xtremespb/frank/hardware/frank_rm1z/3D/Mini-DIN-6P.step

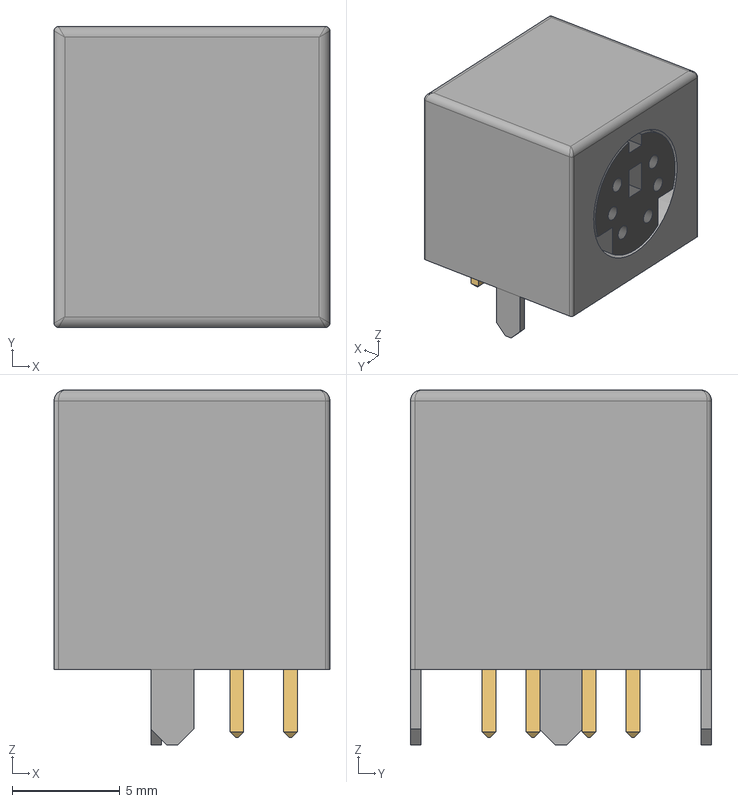
[picture p15: CAD file, 2024-08-21]
hardware/frank_rm1z/3D/Mini-DIN-6P.step
12.8 x 14.0 x 16.5 mm
