xtremespb/frank/hardware/frank_rm1z/3D/SJ1-3535NG.stp

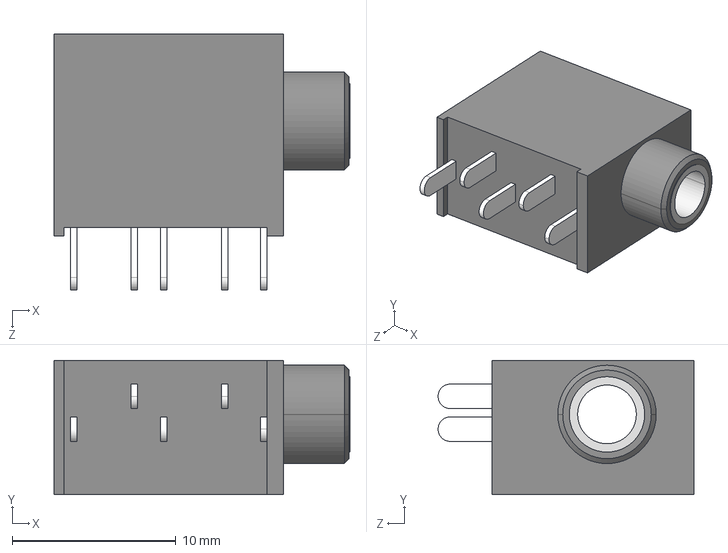
[picture p16: CAD file, 2024-08-21]
hardware/frank_rm1z/3D/SJ1-3535NG.stp
18.1 x 8.20 x 15.6 mm
