xtremespb/frank/hardware/frank_m2/DOCS/HR3FQ.pdf

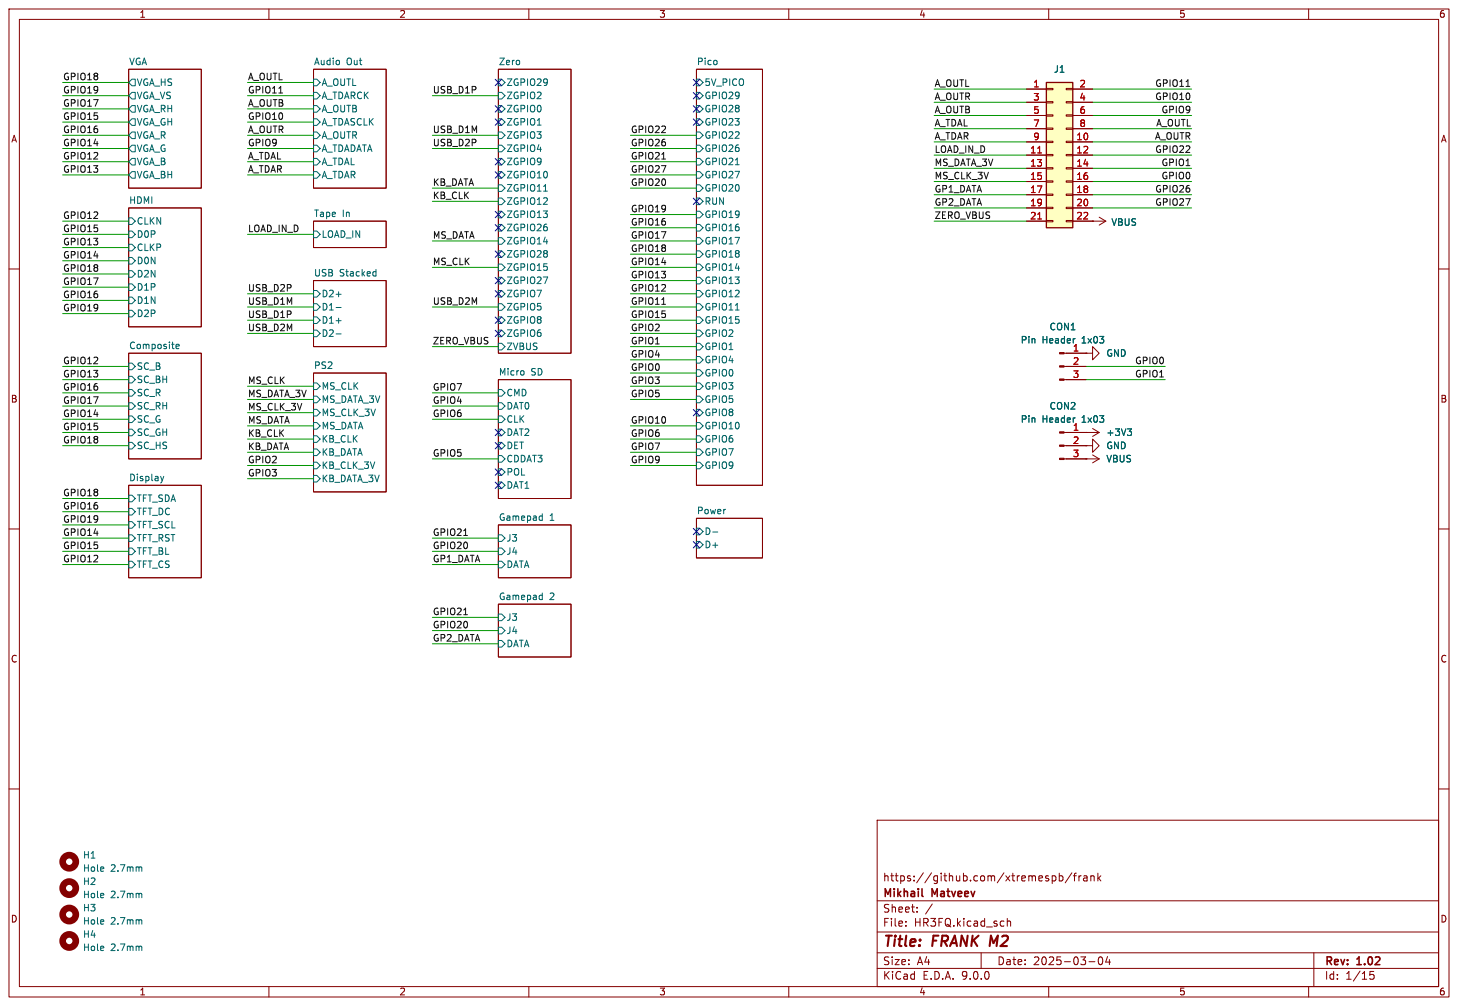
[picture p76: page 1]

ZERO_VBUS
DAT0 CLK DAT2 DET CDDAT3 POL DAT1 Micro SD

https://github.com/xtremespb/frank

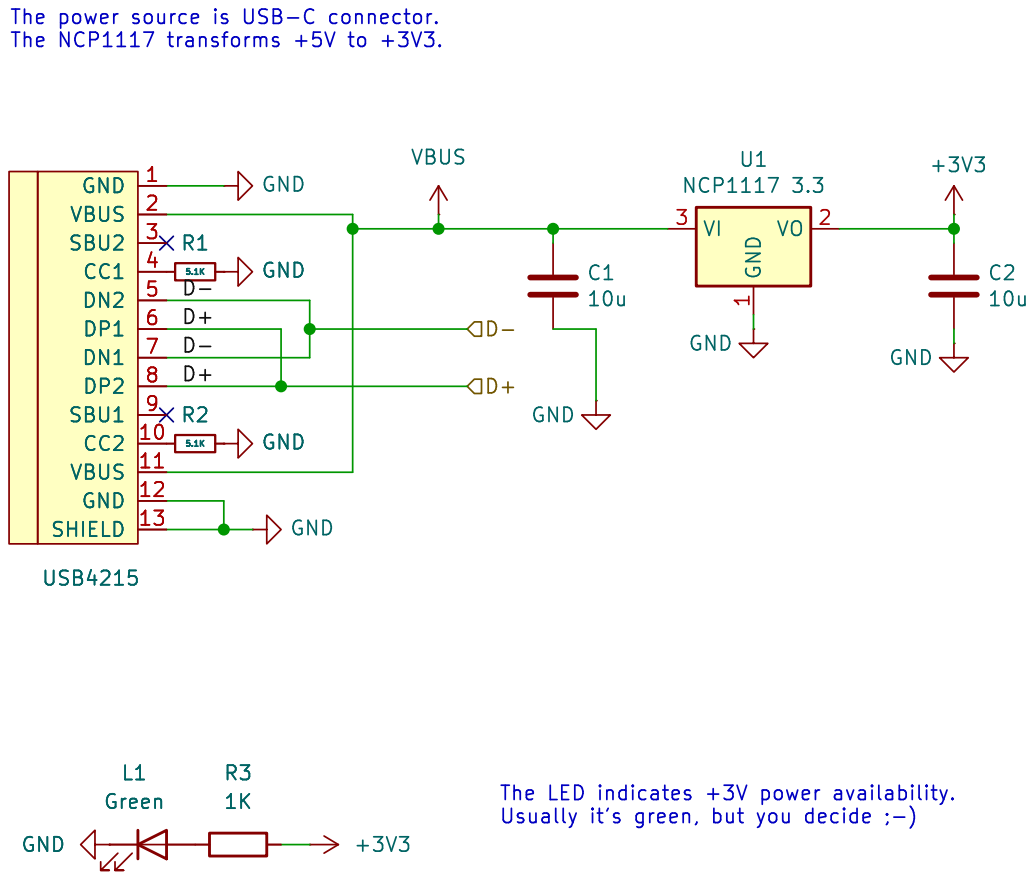
[picture p77: page 2]

1 VO 2 U1 GND NCP1117 3.3 D- D+ D+D+D- D- The power source is USB-C connector. The NCP1117 transforms +5V to +3V3. The LED indicates +3V power availability.
1K GND

Usually it's green, but you decide ;-) GND GND

https://github.com/xtremespb/frank

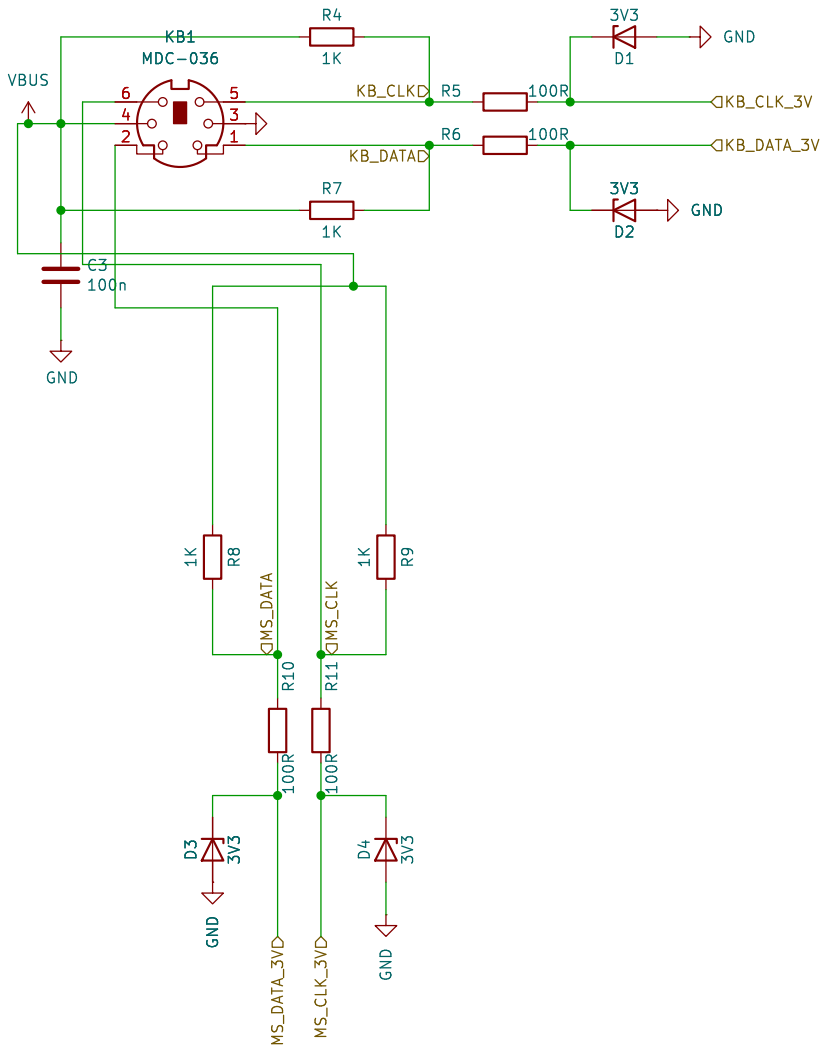
[picture p78: page 3]

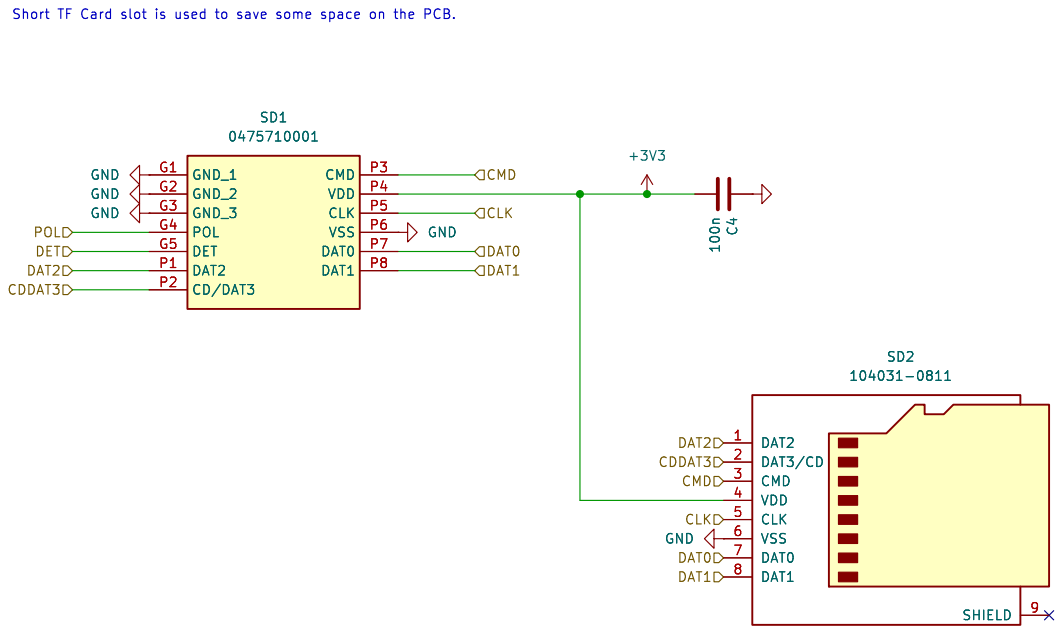
[picture p79: page 4]

https://github.com/xtremespb/frank


https://github.com/xtremespb/frank


https://github.com/xtremespb/frank

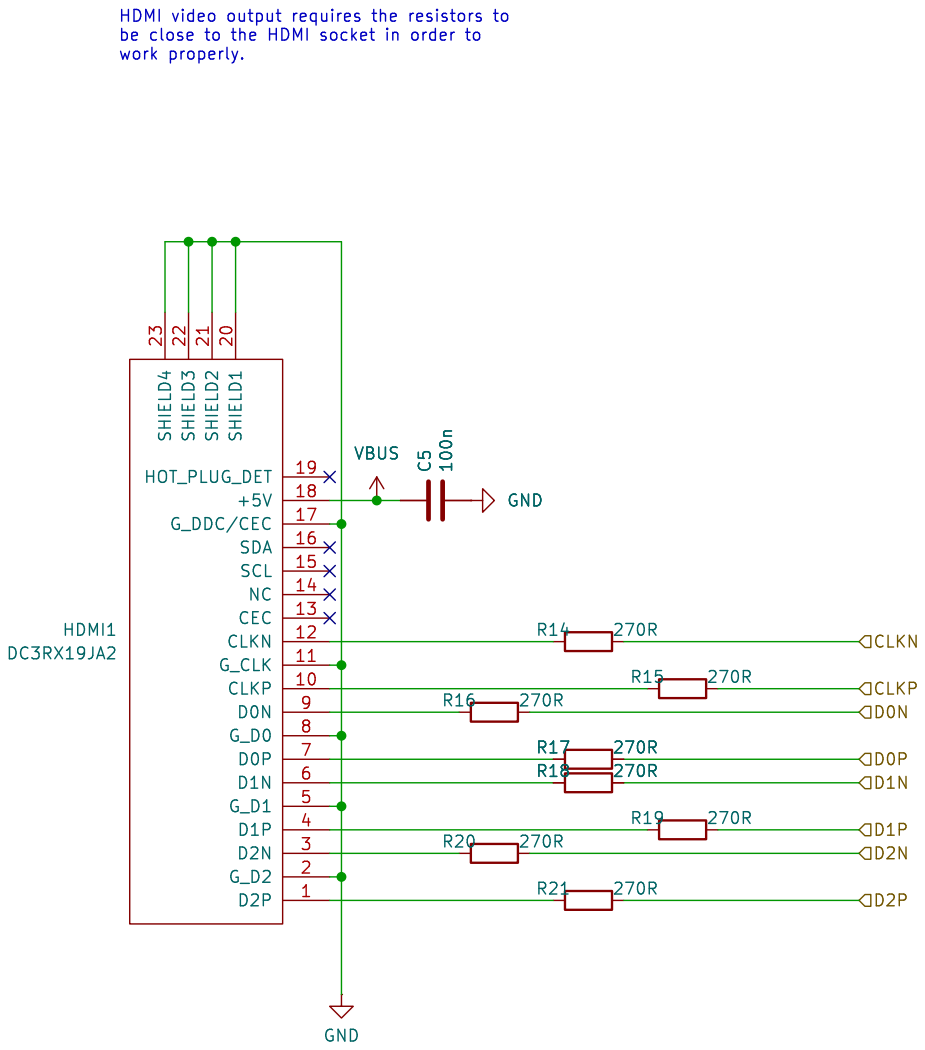
[picture p80: page 7]

https://github.com/xtremespb/frank


https://github.com/xtremespb/frank

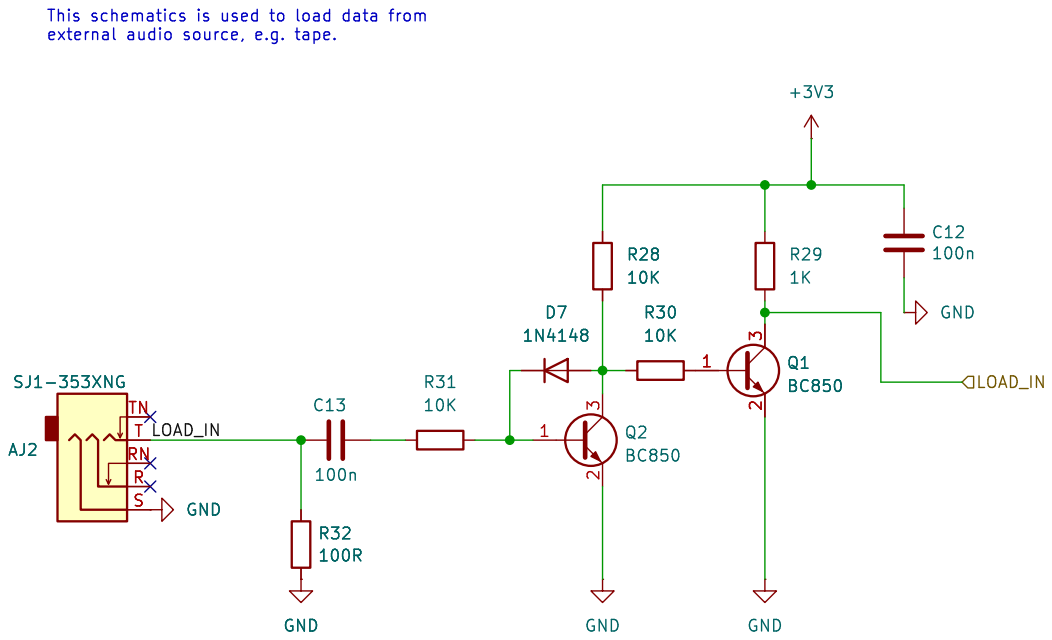
[picture p81: page 9]

https://github.com/xtremespb/frank

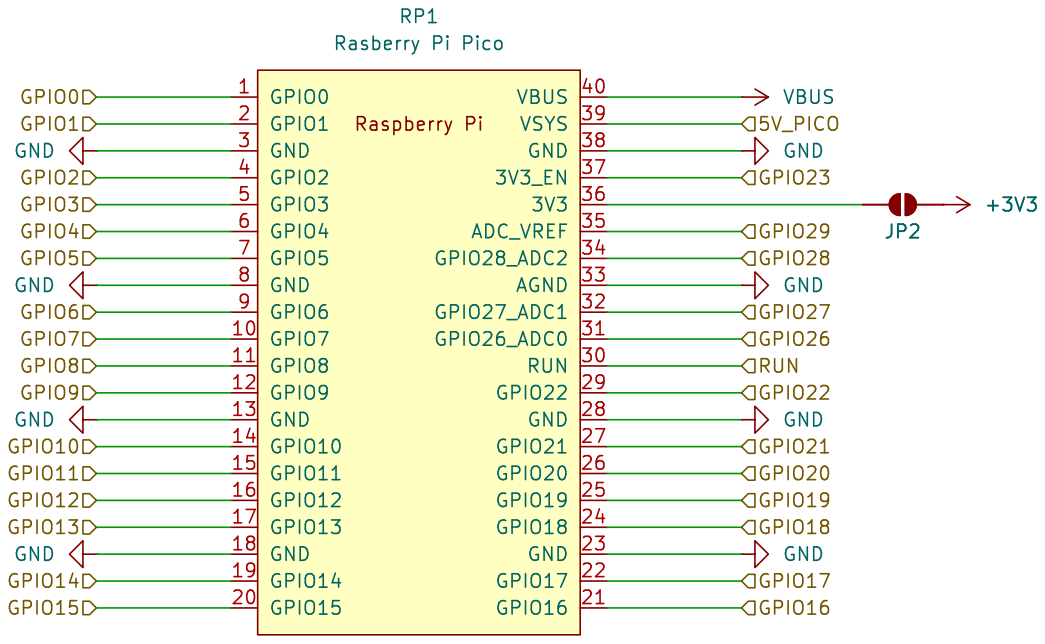
[picture p82: page 10]

https://github.com/xtremespb/frank


https://github.com/xtremespb/frank


https://github.com/xtremespb/frank


https://github.com/xtremespb/frank


https://github.com/xtremespb/frank


https://github.com/xtremespb/frank
