xtremespb/frank/hardware/hdmi2vga/DOCS/assembly.pdf

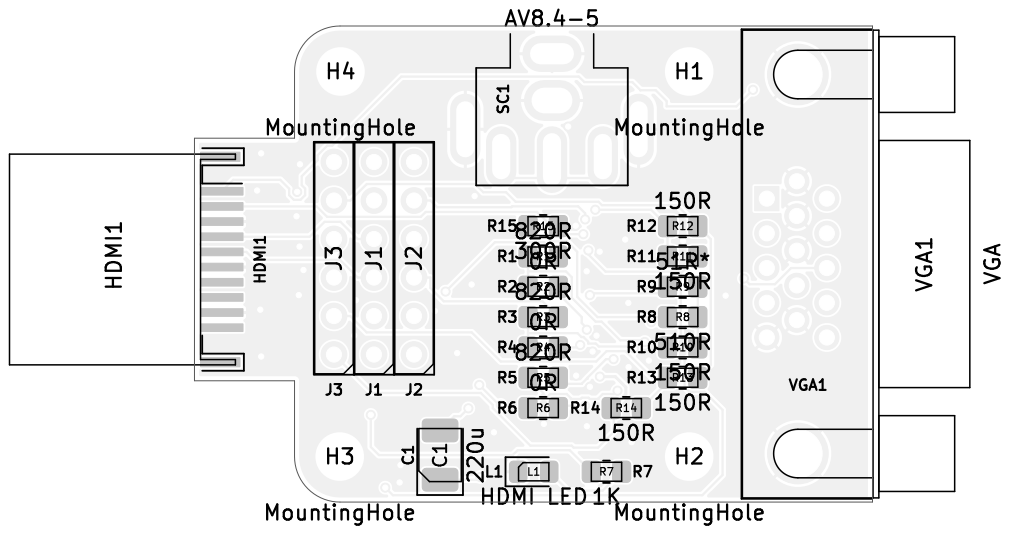
[picture p83: page 1]

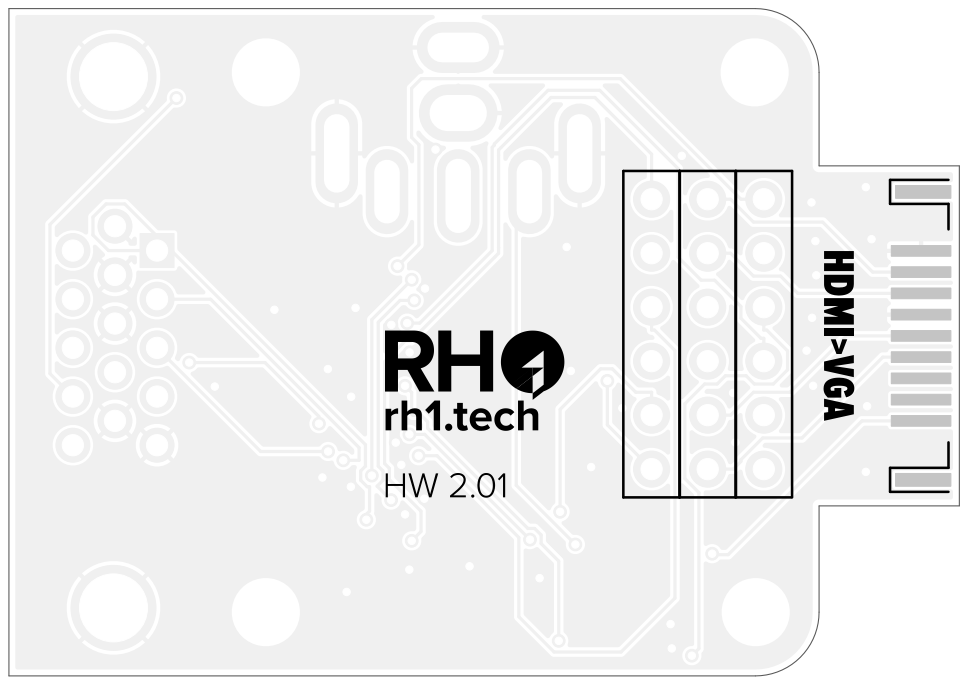
[picture p84: page 2]
D Date: 2025-03-04 KiCad; E.D.A. 9.0.0 Size: A4; Rev: 2.01; Id: /1 Title: HDMI to VGA Passive Adapter File: hdmi2vgaP.kicad_pcb Sheet: Black; And; White; BOT Mikhail; Matveev; https://github.com/xtremespb/frank Black; BOT -; Page 2/2
