xtremespb/frank/hardware/minifrank_rm1/DOCS/minifrank.pdf

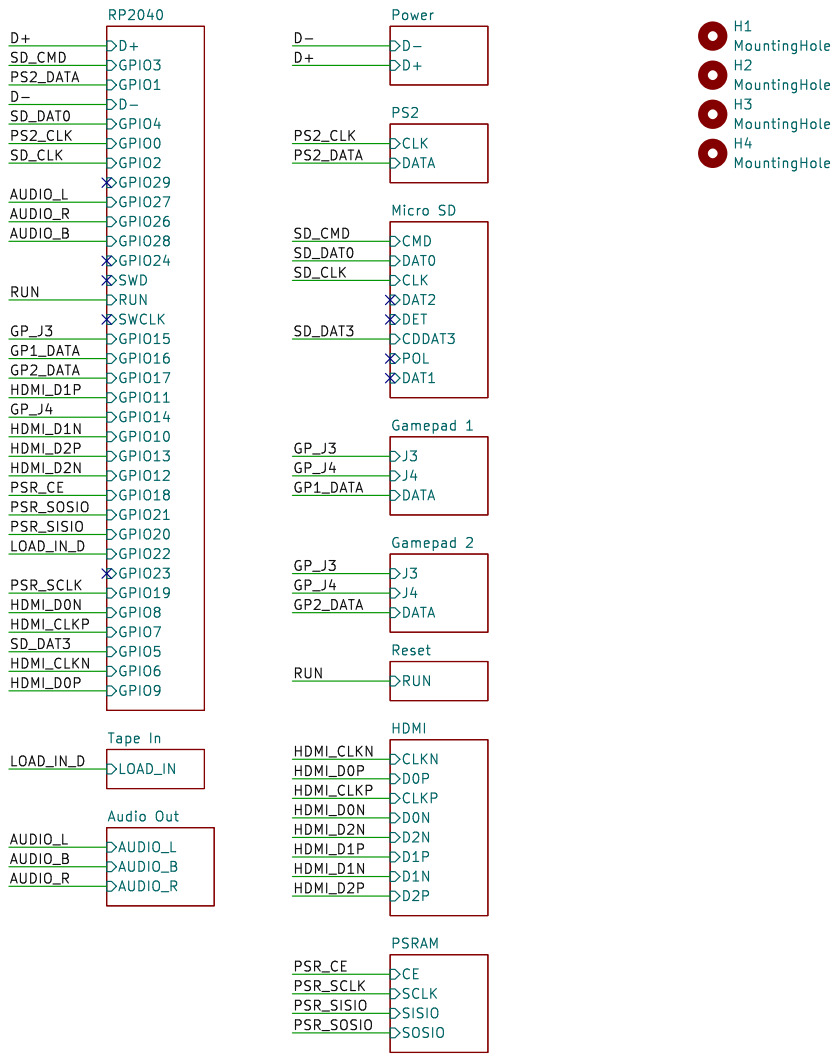
[picture p85: page 1]

H1 MountingHole H2 MountingHole H3 MountingHole H4 MountingHole AUDIO_R
SD_CMD

https://github.com/xtremespb/frank

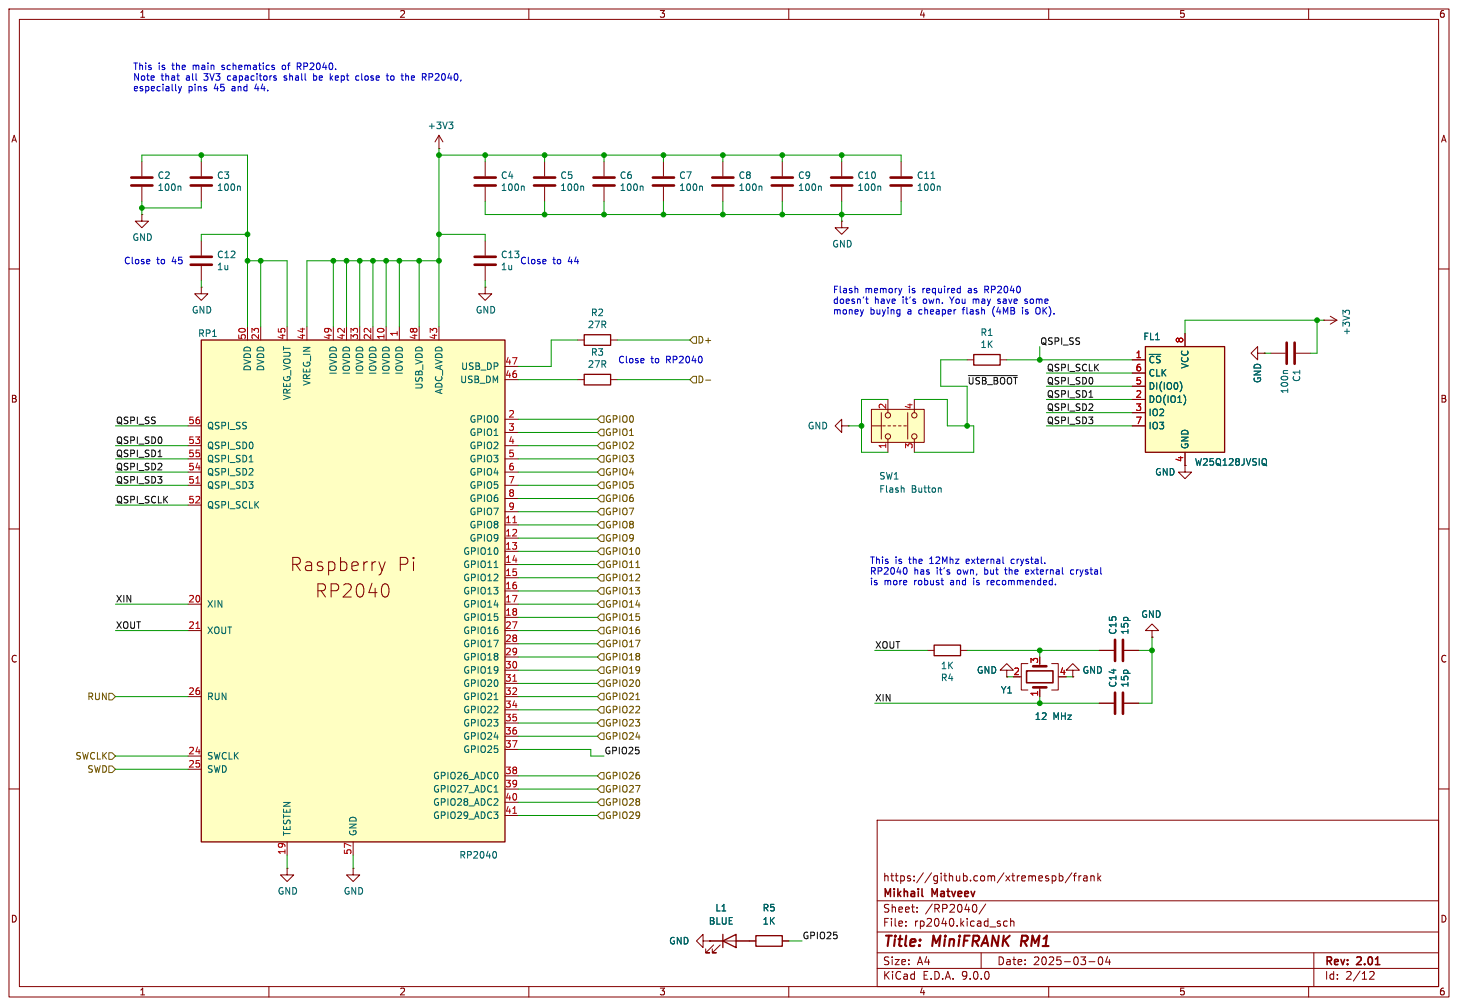
[picture p86: page 2]

https://github.com/xtremespb/frank

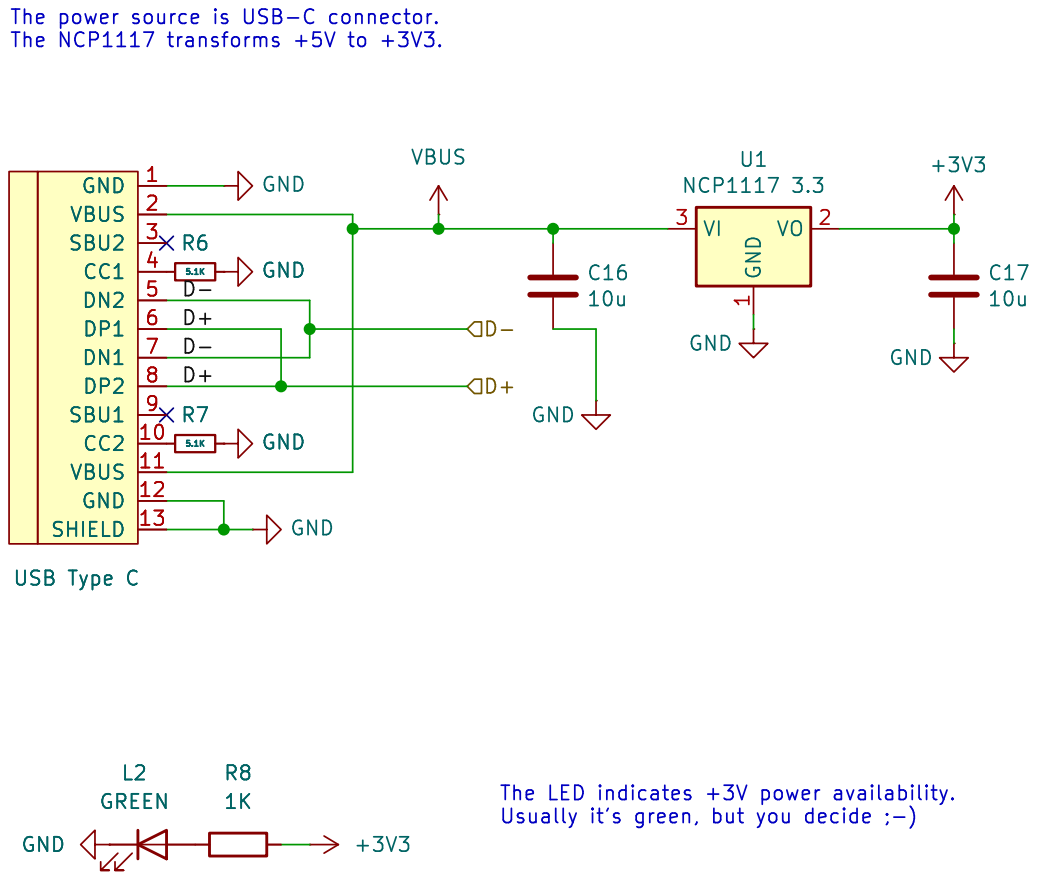
[picture p87: page 3]

https://github.com/xtremespb/frank

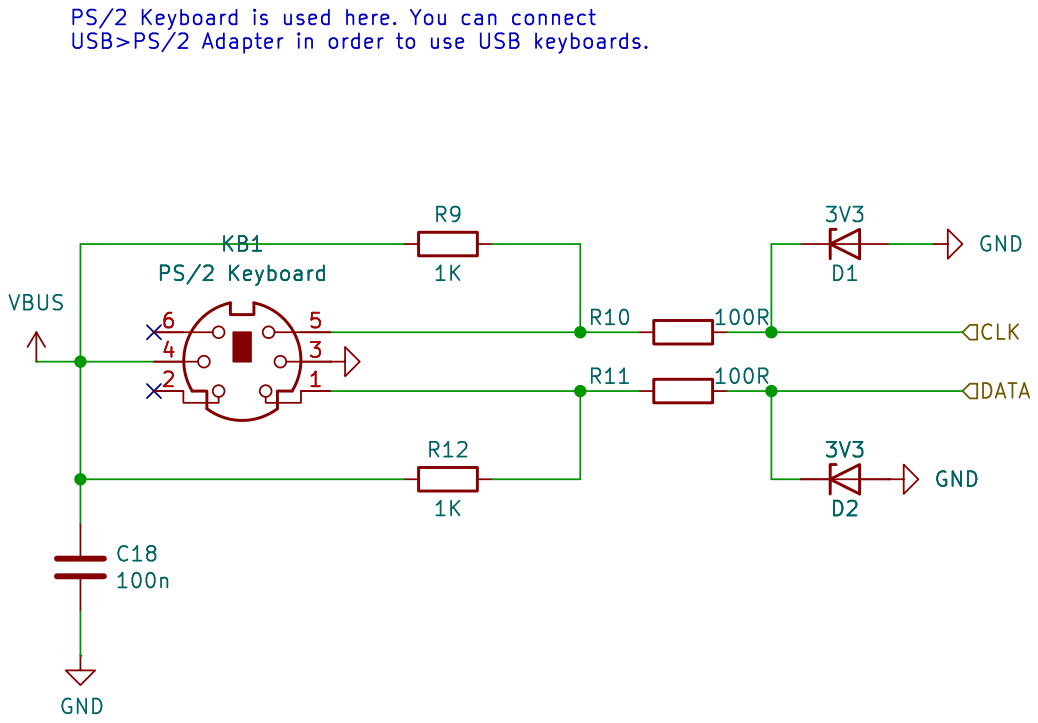
[picture p88: page 4]

https://github.com/xtremespb/frank

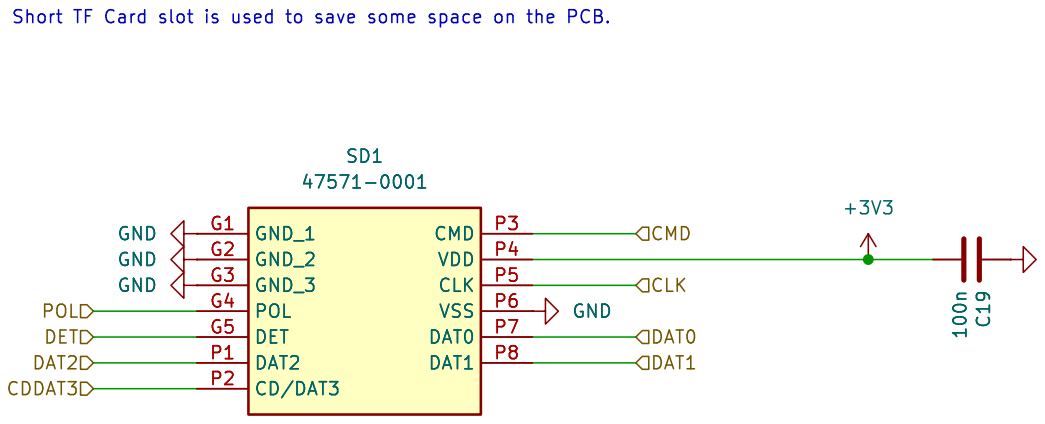
[picture p89: page 5]

https://github.com/xtremespb/frank

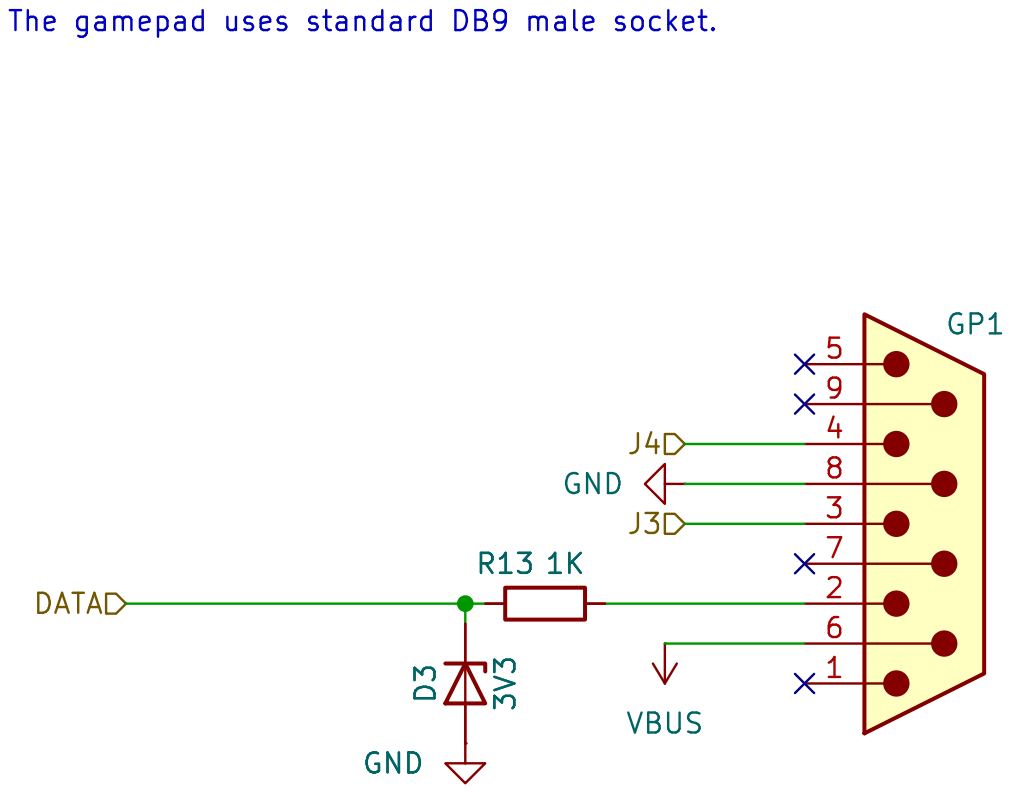
[picture p90: page 6]

https://github.com/xtremespb/frank

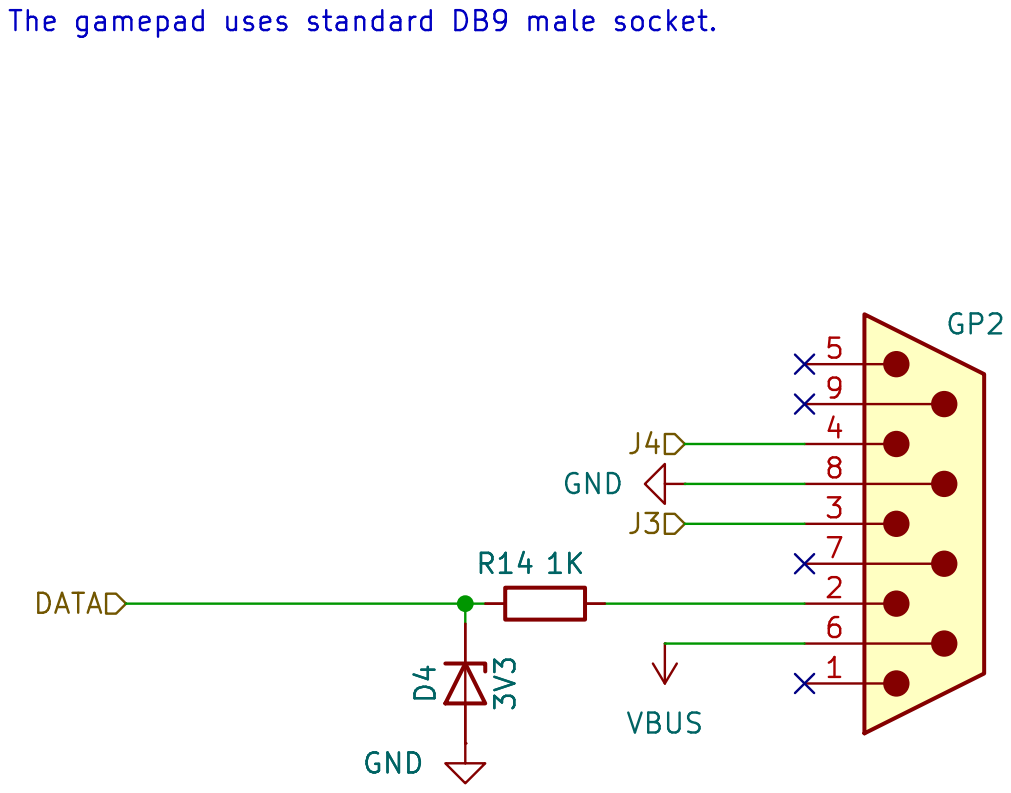
[picture p91: page 7]

https://github.com/xtremespb/frank

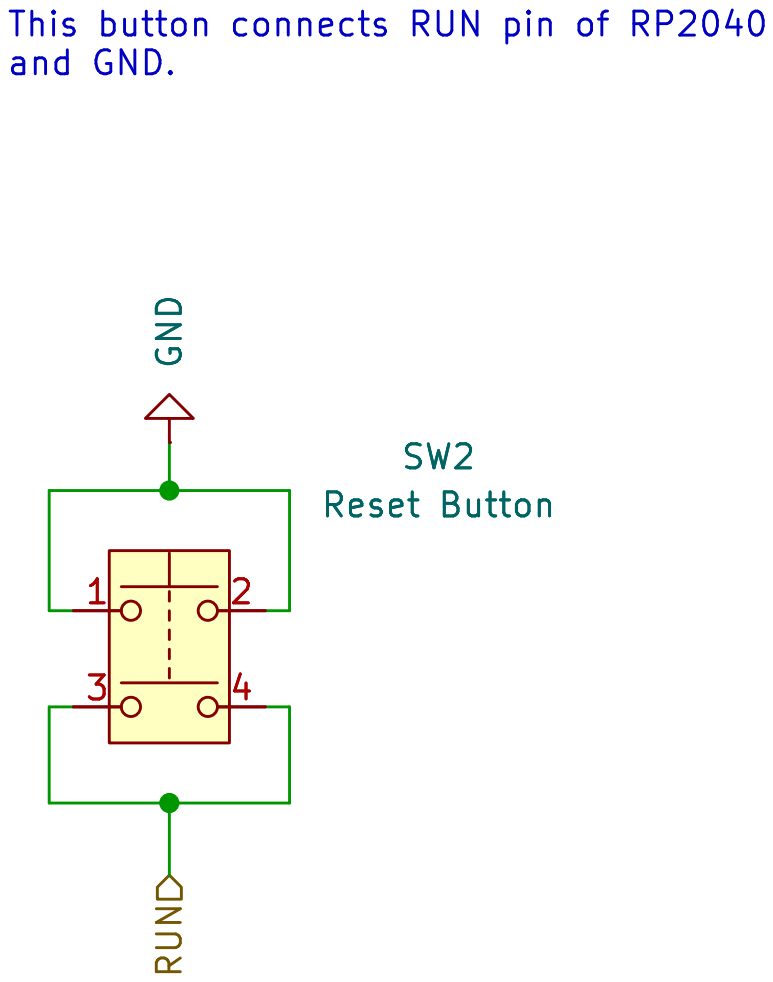
[picture p92: page 8]

https://github.com/xtremespb/frank

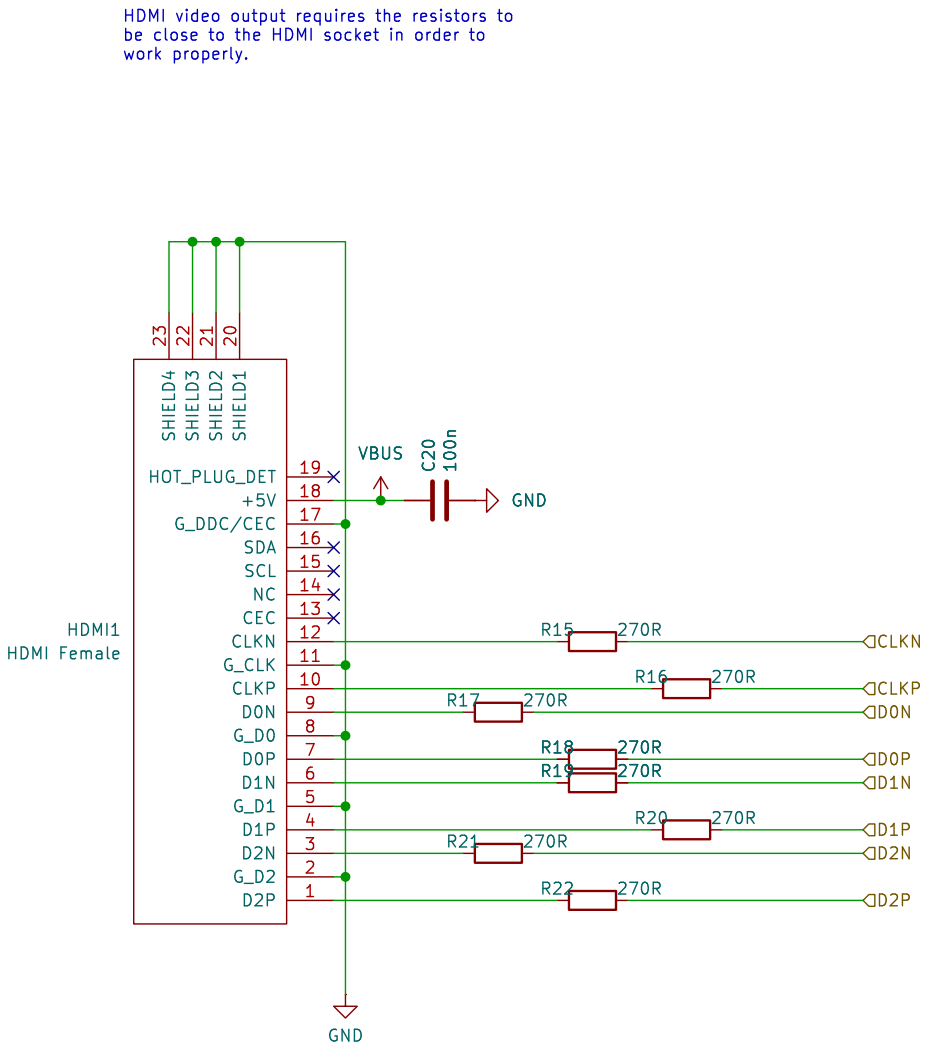
[picture p93: page 9]

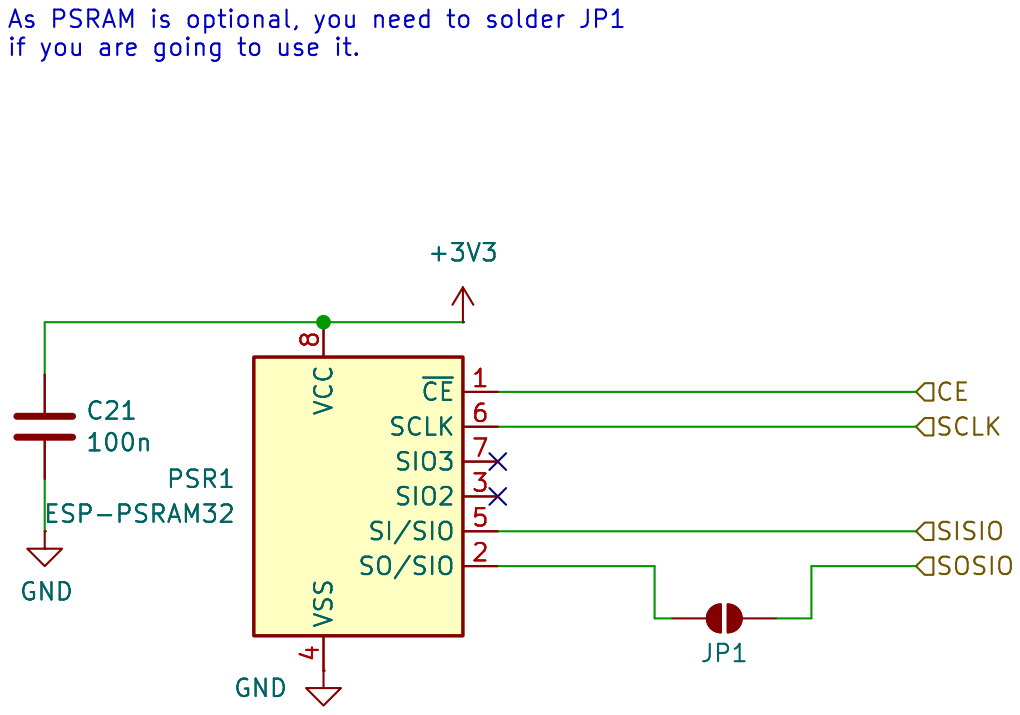
[picture p94: page 10]

if you are going to use it. GND

4 ~{CE}1 SCLK 6 SIO3 7 SIO2 3 SI/SIO 5 SO/SIO 2 PSR1 ESP-PSRAM32 GND

4 ~{CE}1 SCLK 6 SIO3 7 SIO2 3 SI/SIO 5 SO/SIO 2 GND

https://github.com/xtremespb/frank

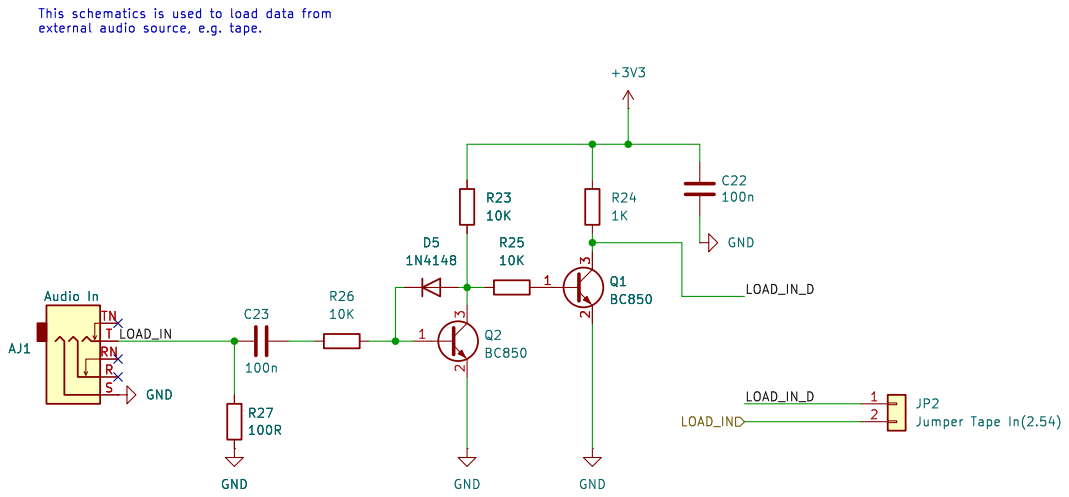
[picture p95: page 11]

https://github.com/xtremespb/frank

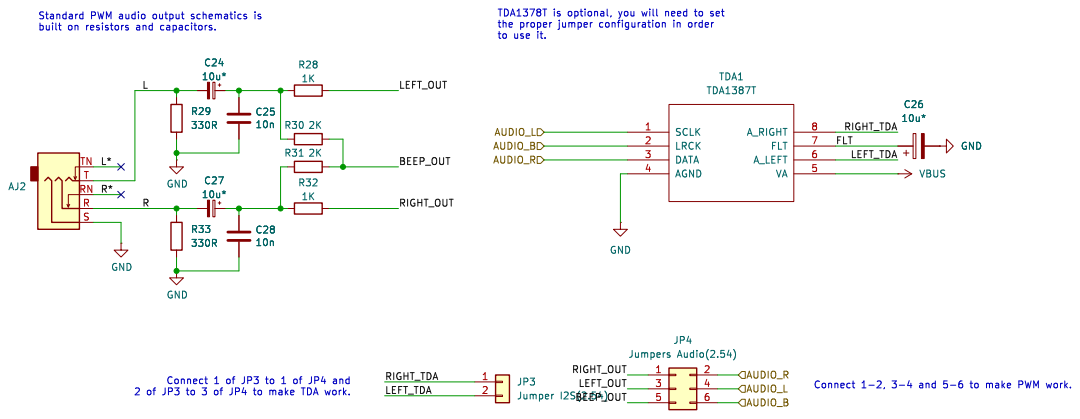
[picture p96: page 12]

to use it. Connect 1 of JP3 to 1 of JP4 and

https://github.com/xtremespb/frank
