xtremespb/frank/hardware/turbofrank/DOCS/turbofrank.pdf

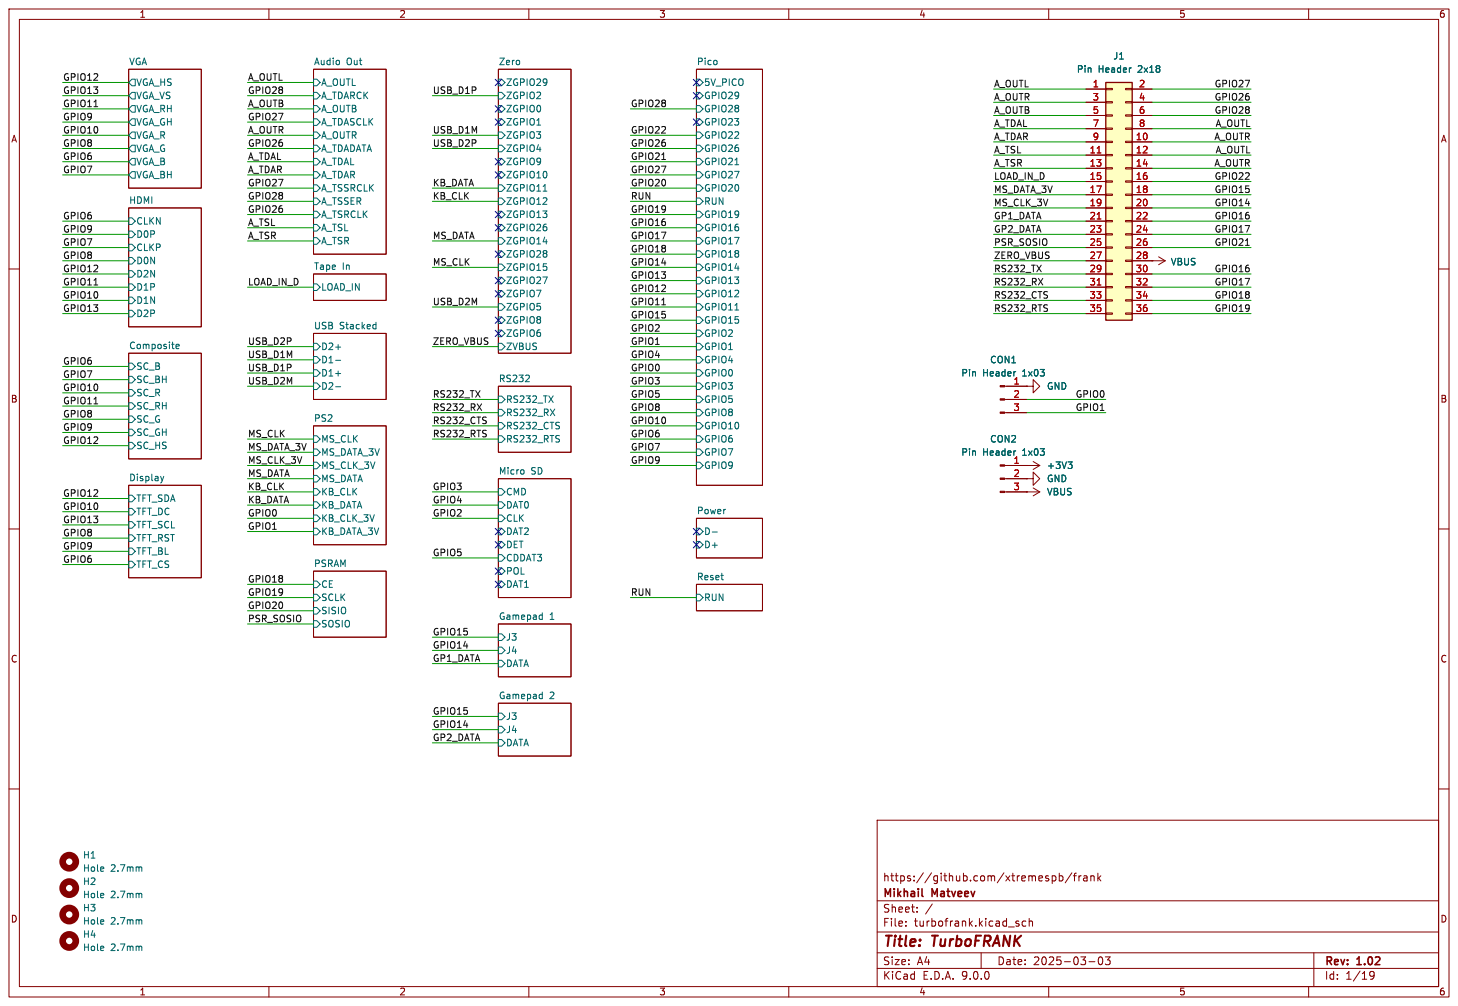
[picture p97: page 1]

J1 Pin Header 2x18 VBUS H3 Hole 2.7mm

DAT0 CLK DAT2 DET CDDAT3 POL DAT1 Micro SD

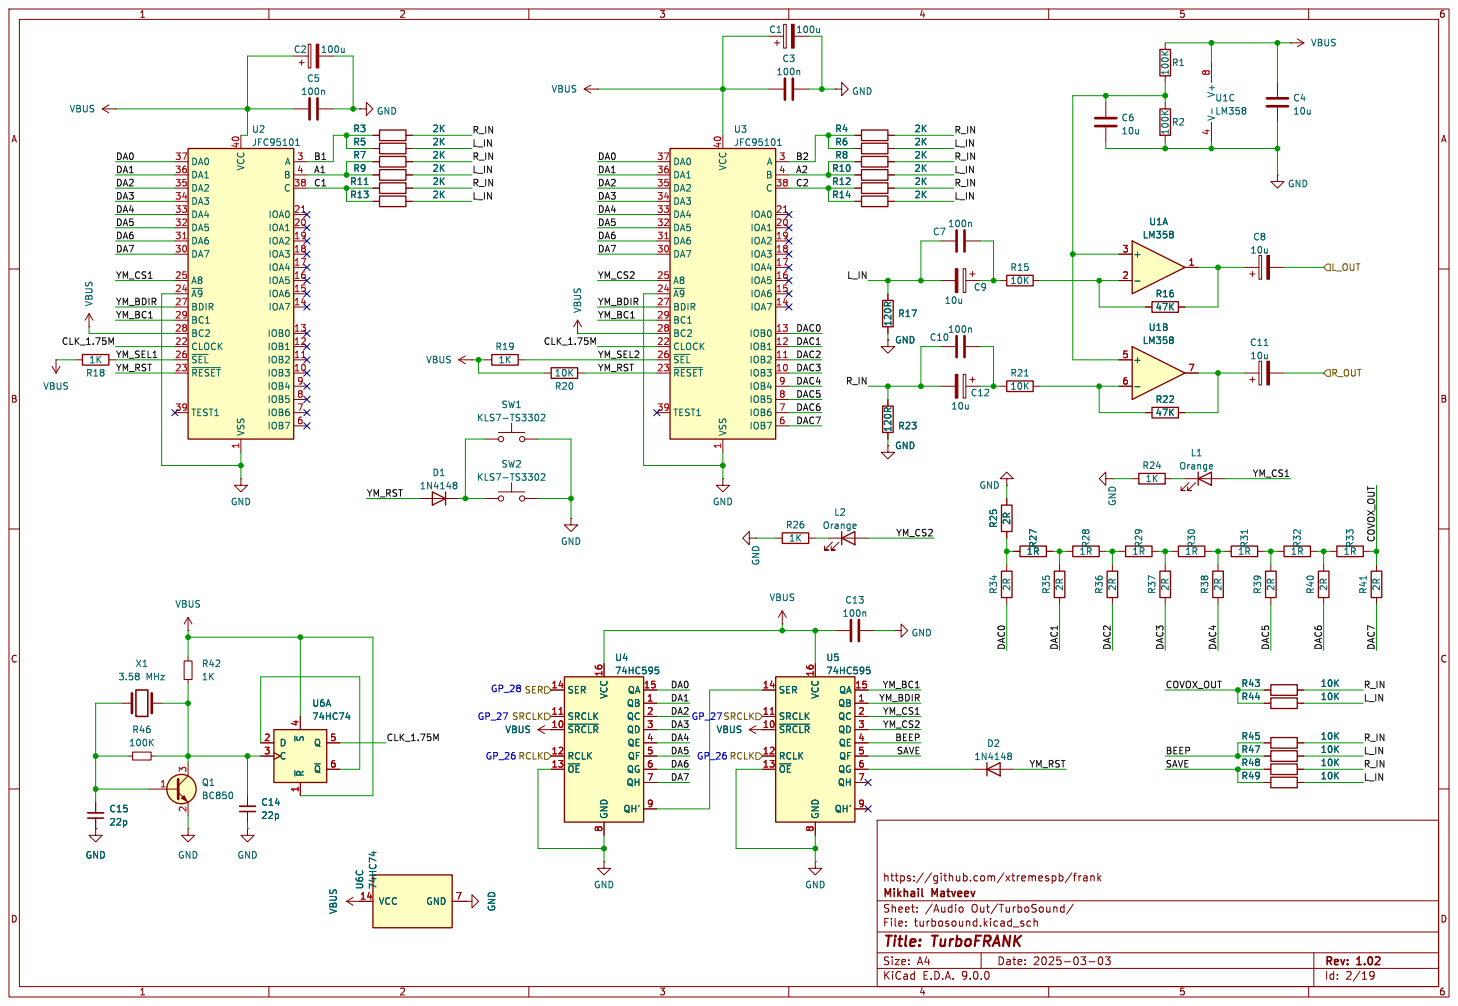
[picture p98: page 2]

8 QA 15 QB 1 QC 2 QD 3 QE 4 QF 5 QG 6 QH 7 QH' 9 VBUSU6C 74HC74 VCC 14 GND 7 GND R25 2R

SER

8 QA 15 QB 1 QC 2 QD 3 QE 4 QF 5 QG 6 QH 7 QH' 9 VBUS R45 10K R49 10K R47 10K R48 10K R44 10K R43 10K

https://github.com/xtremespb/frank

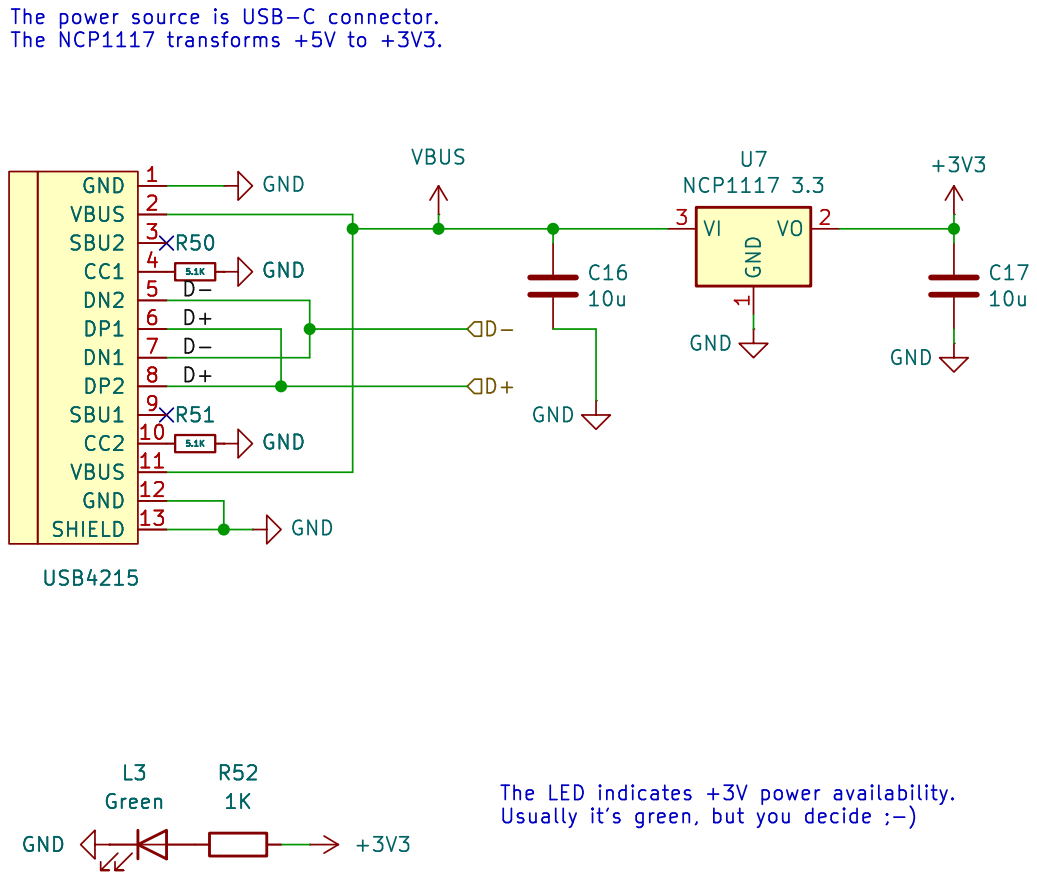
[picture p99: page 3]

1 VO 2 U7 NCP1117 3.3 +3V3 D- D+ D- D- D+D+ The power source is USB-C connector. The NCP1117 transforms +5V to +3V3. The LED indicates +3V power availability.

Usually it's green, but you decide ;-) GND

https://github.com/xtremespb/frank

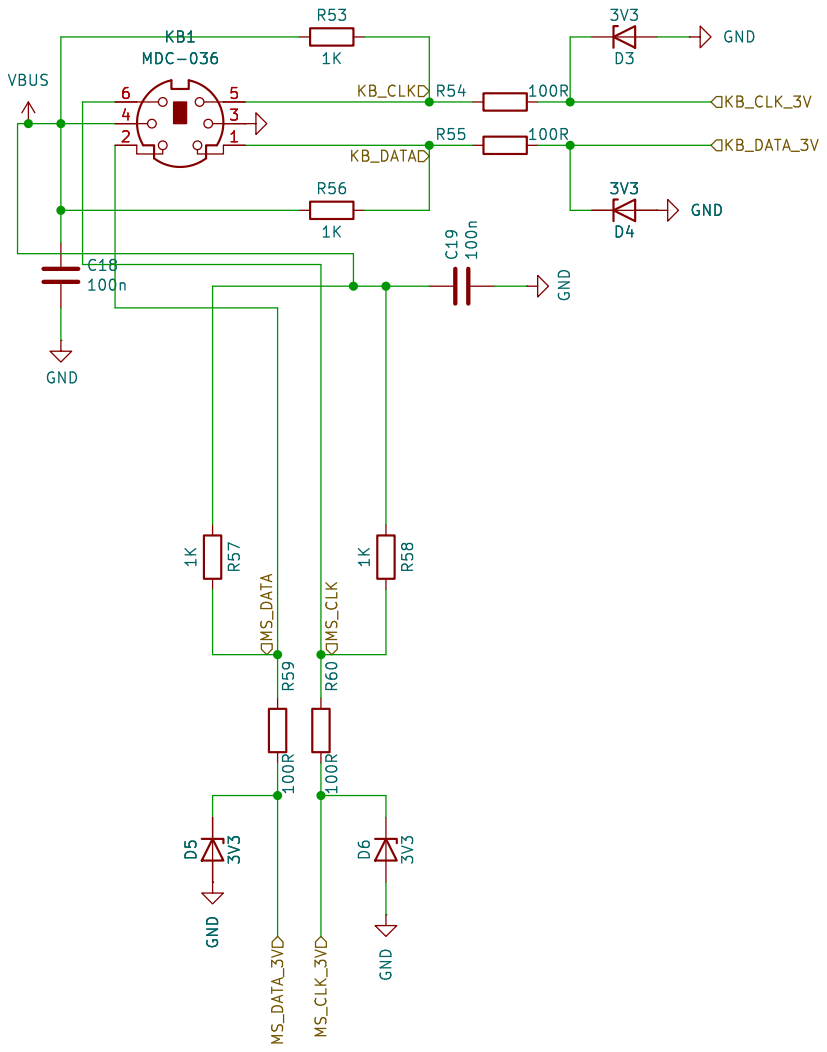
[picture p100: page 4]

https://github.com/xtremespb/frank

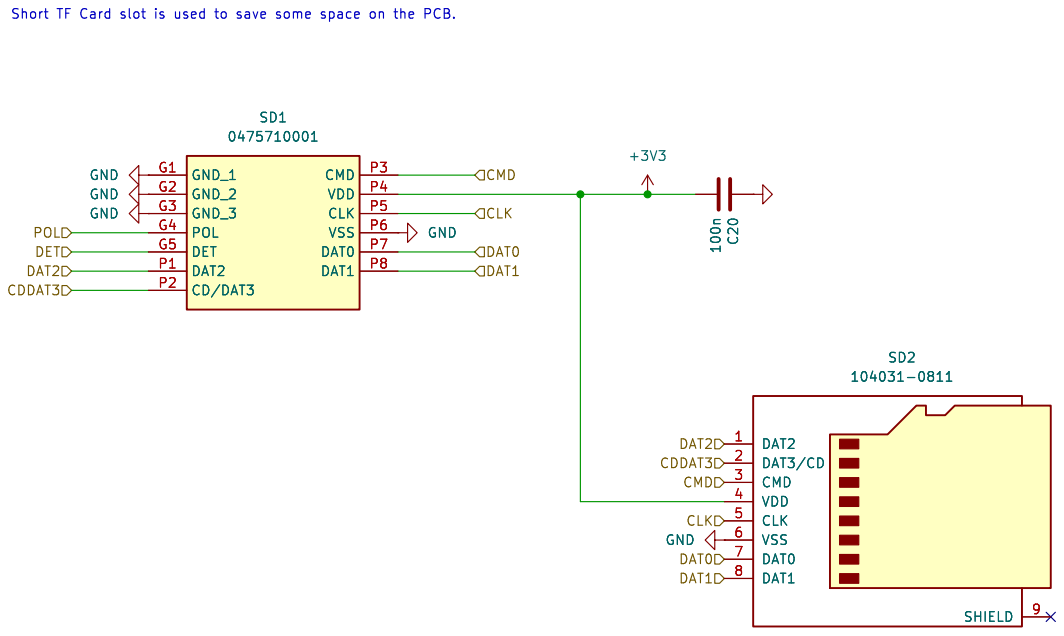
[picture p101: page 5]

https://github.com/xtremespb/frank

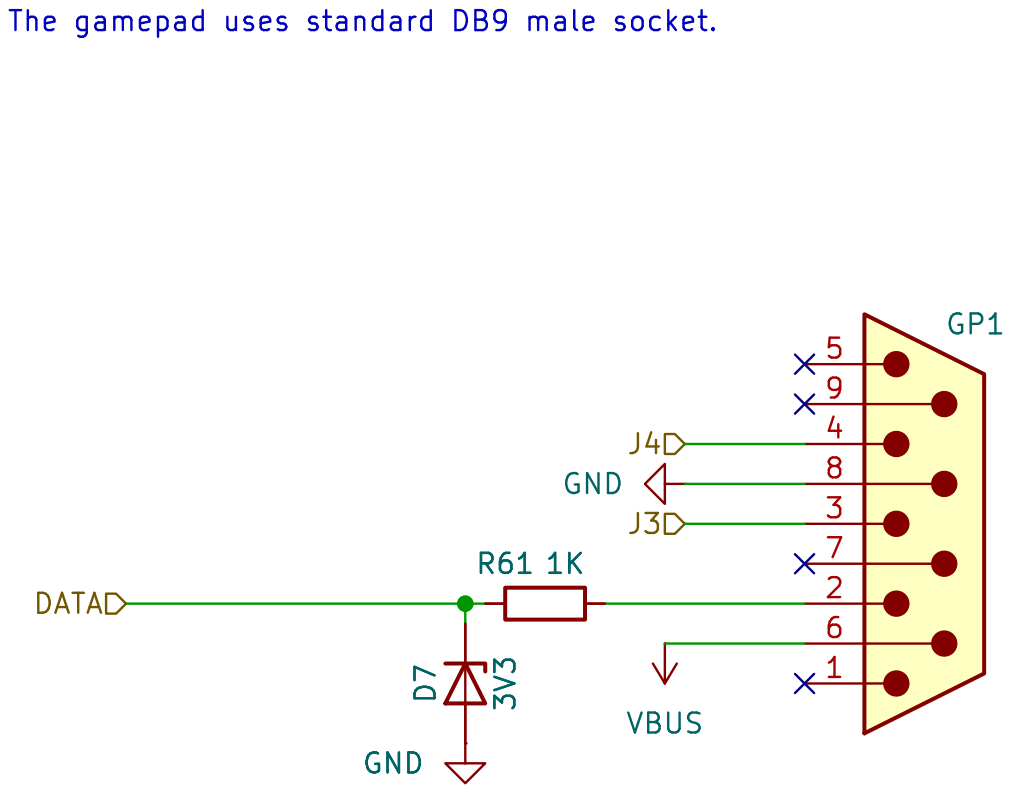
[picture p102: page 6]

https://github.com/xtremespb/frank

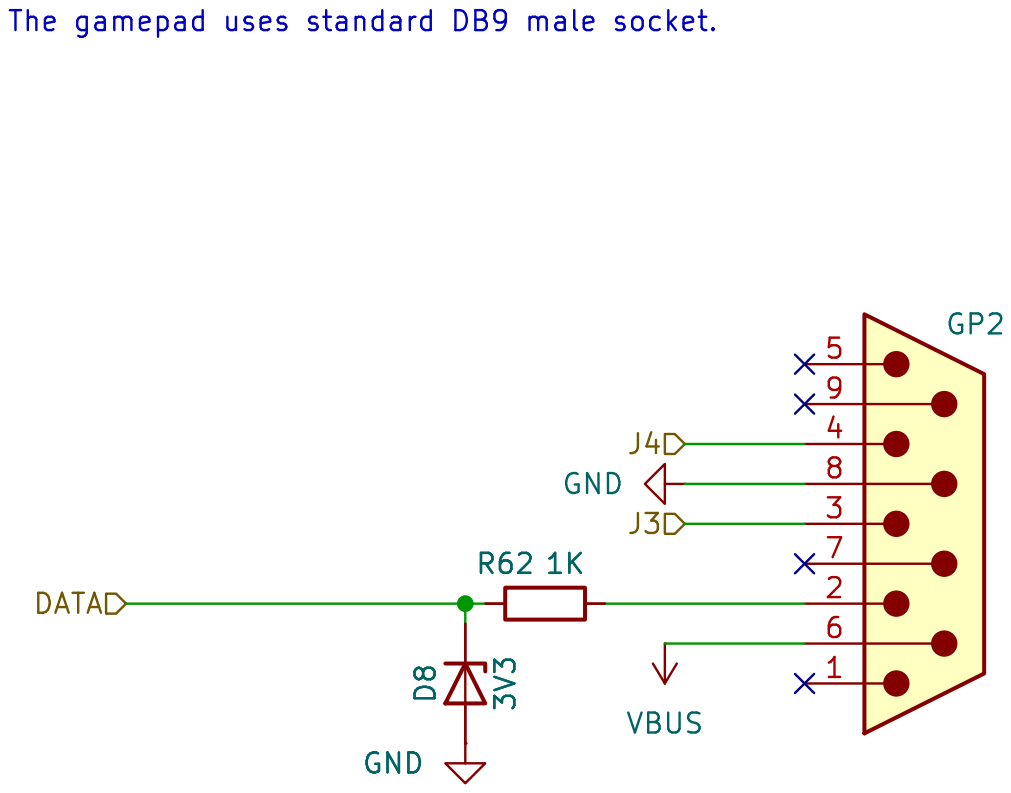
[picture p103: page 7]

https://github.com/xtremespb/frank

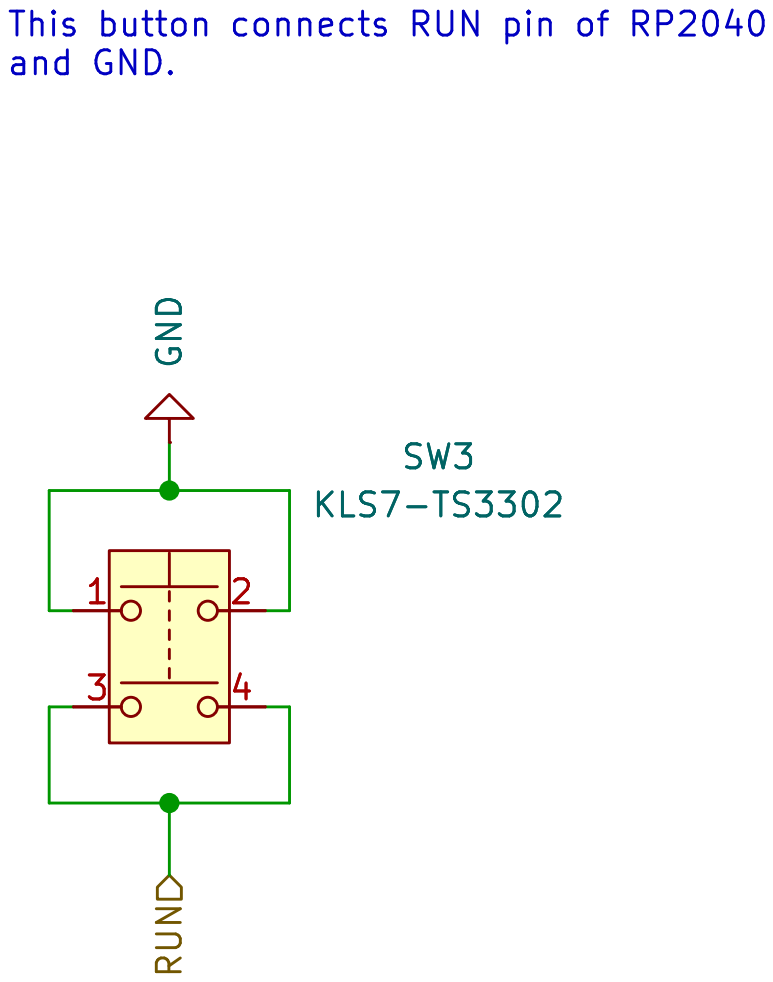
[picture p104: page 8]

https://github.com/xtremespb/frank GND

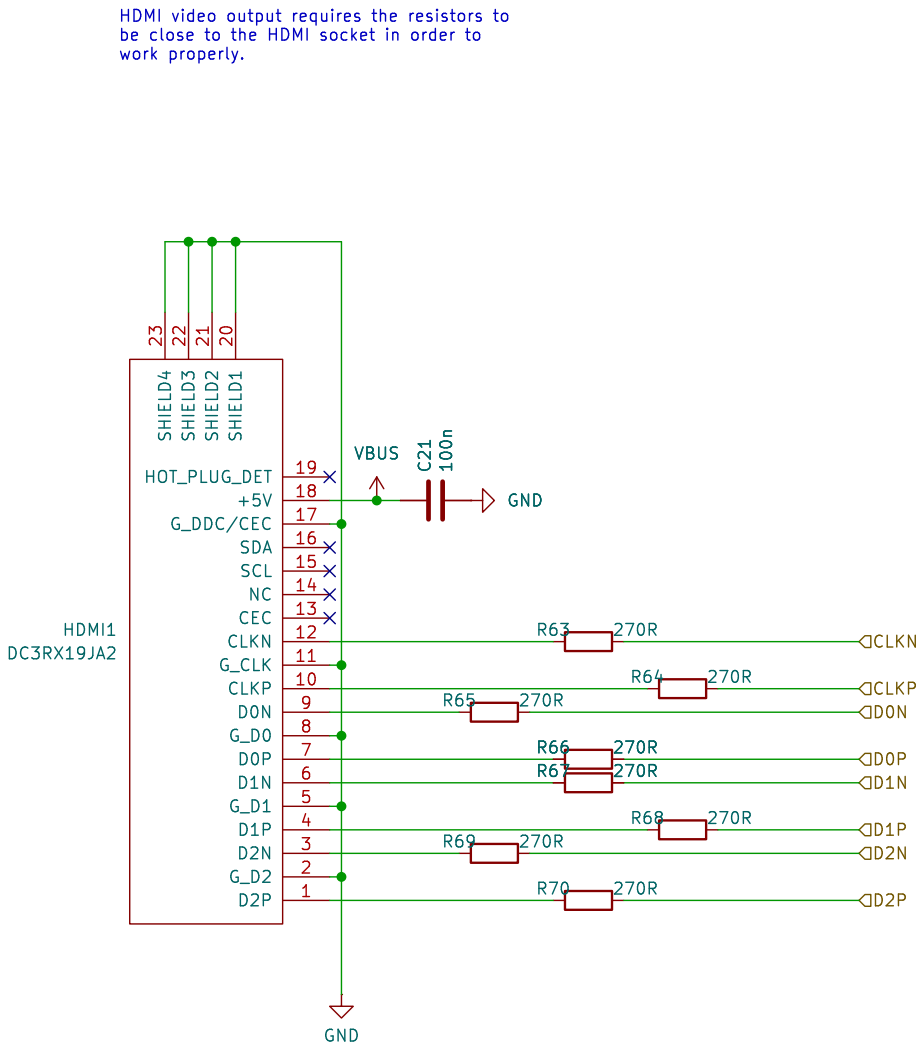
[picture p105: page 9]

https://github.com/xtremespb/frank

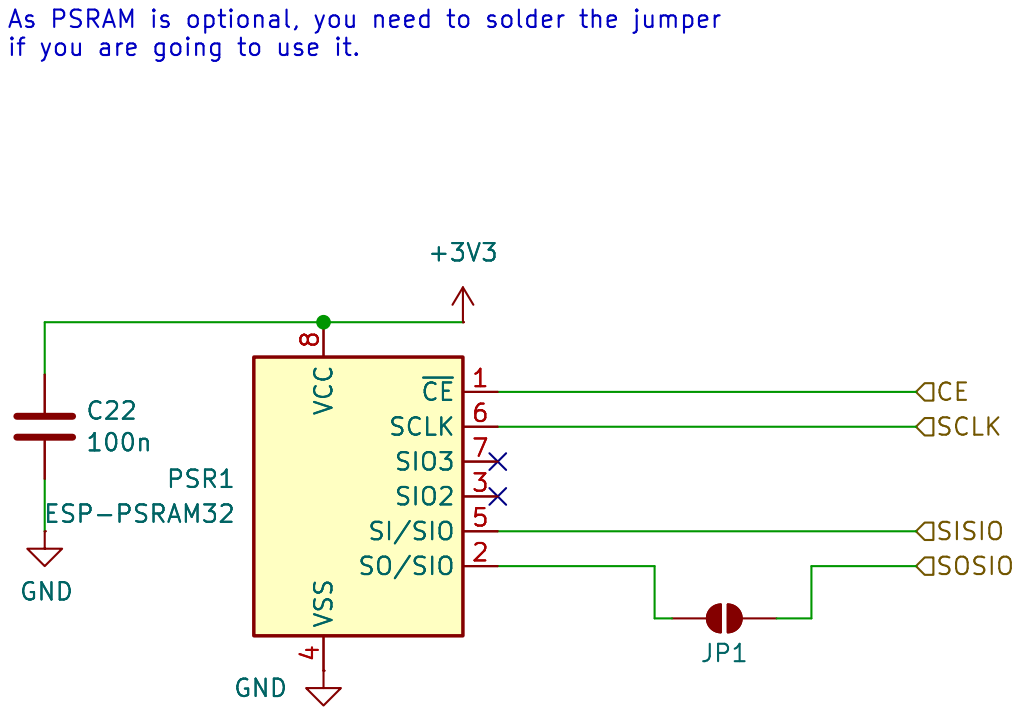
[picture p106: page 10]

4 ~{CE}1 SCLK 6 SIO3 7 SIO2 3 SI/SIO 5 SO/SIO 2 PSR1 ESP-PSRAM32 C22

4 ~{CE}1 SCLK 6 SIO3 7 SIO2 3 SI/SIO 5 SO/SIO 2 C22

https://github.com/xtremespb/frank

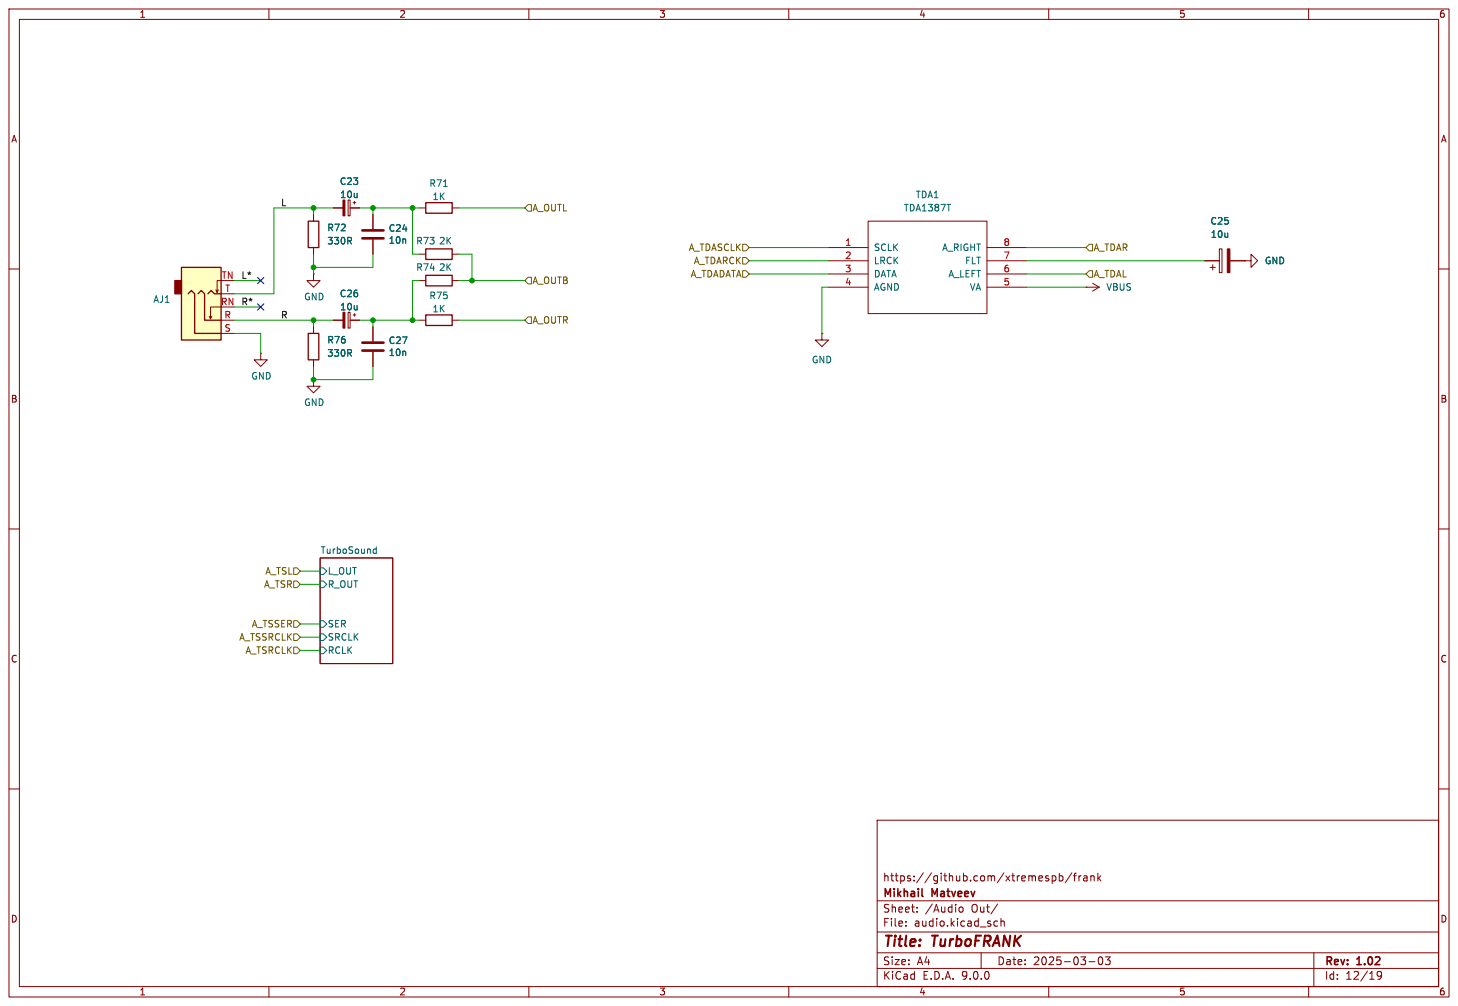
[picture p107: page 11]

https://github.com/xtremespb/frank

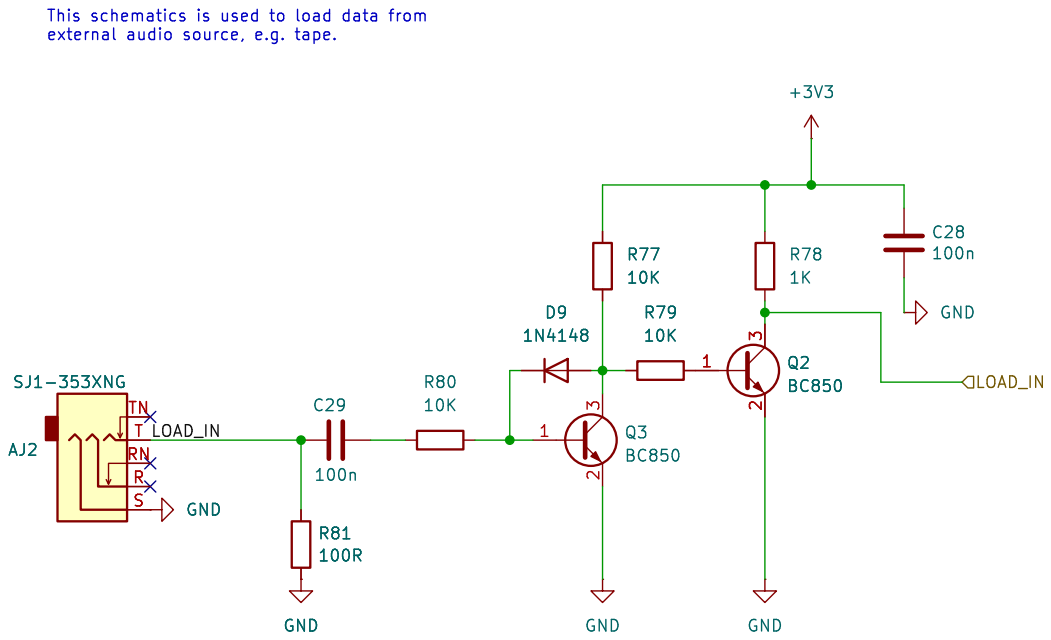
[picture p108: page 12]

https://github.com/xtremespb/frank

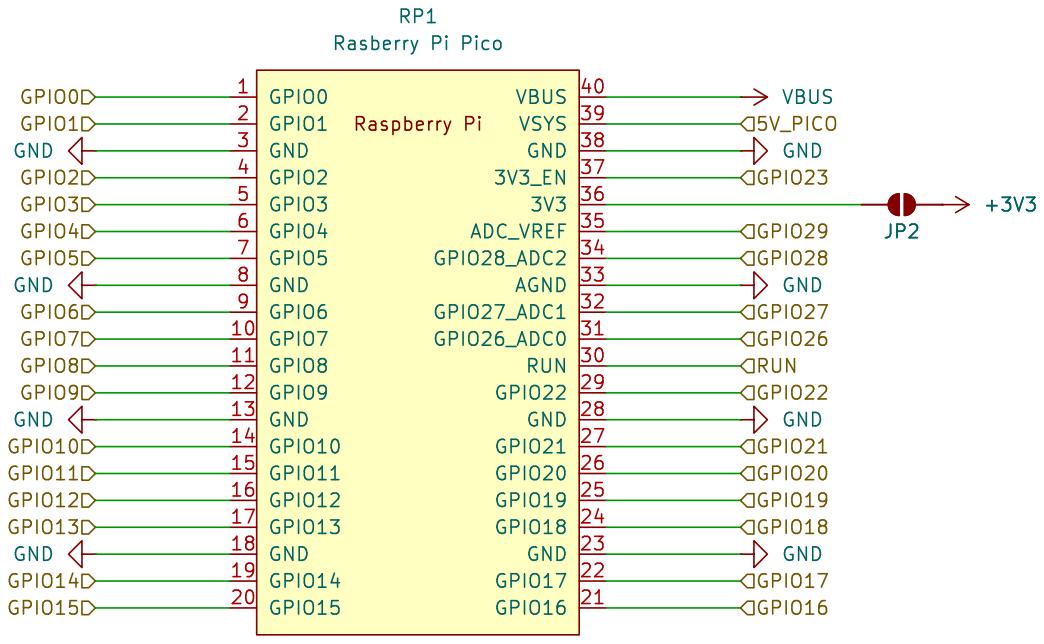
[picture p109: page 13]

https://github.com/xtremespb/frank

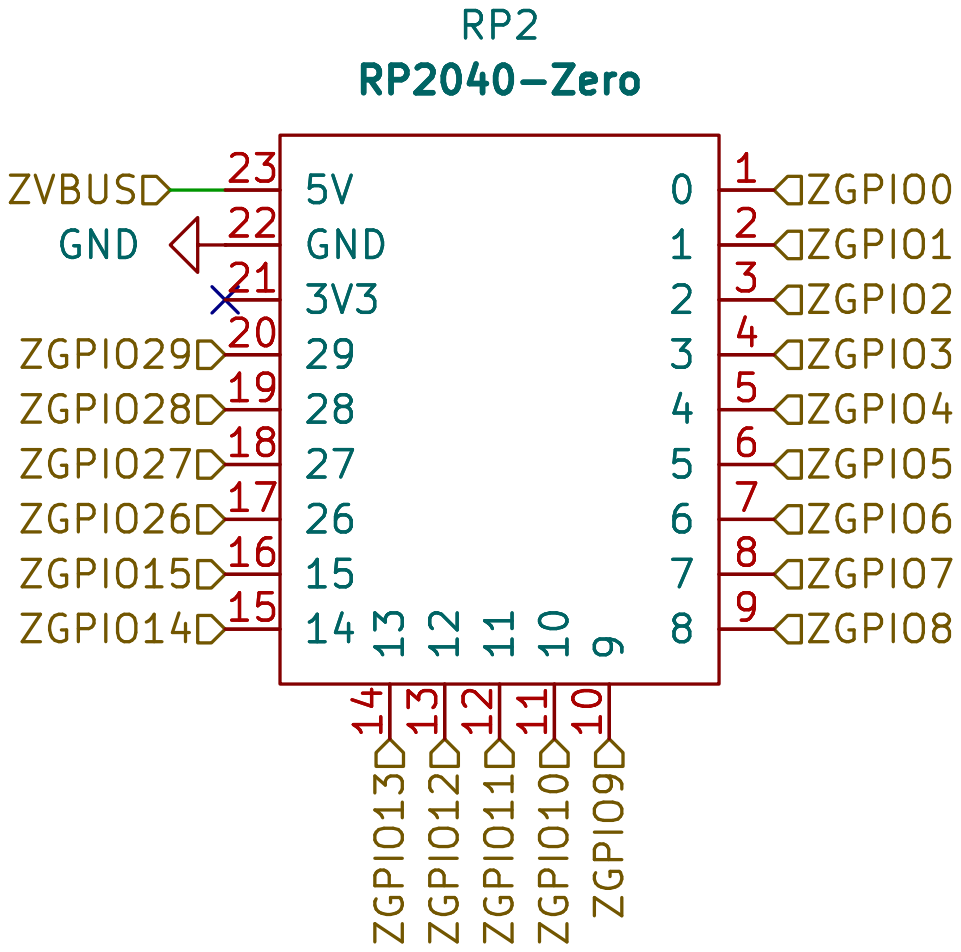
[picture p110: page 14]

https://github.com/xtremespb/frank

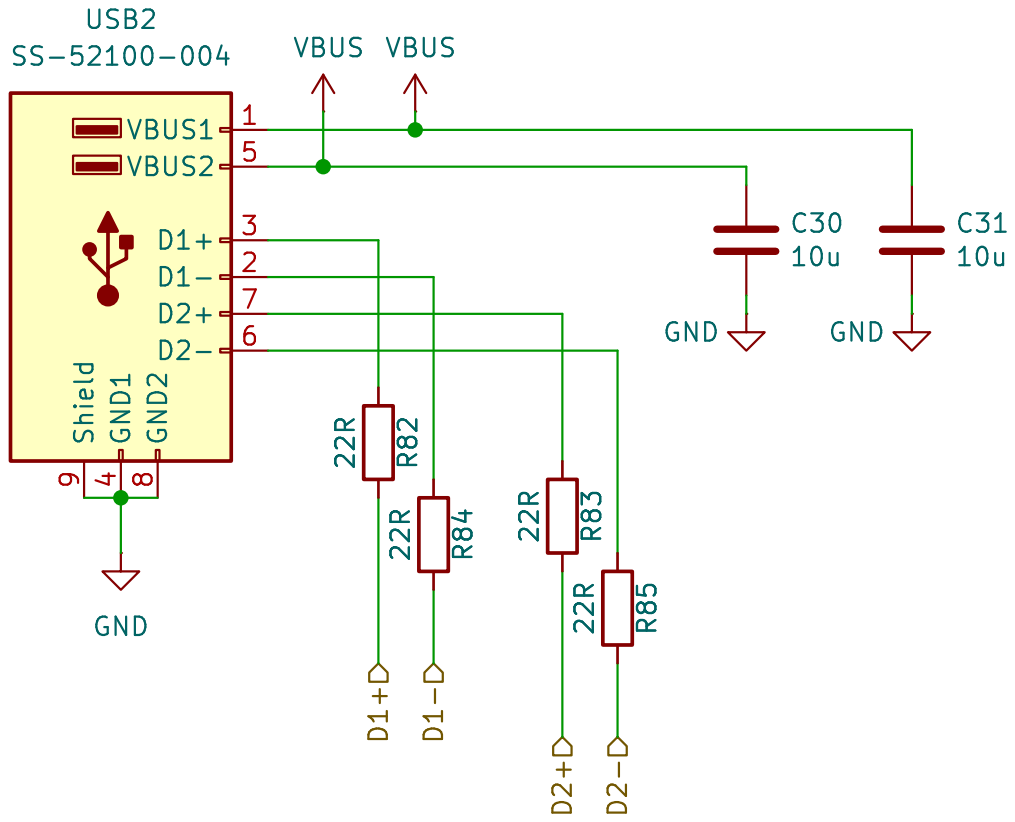
[picture p111: page 15]

https://github.com/xtremespb/frank

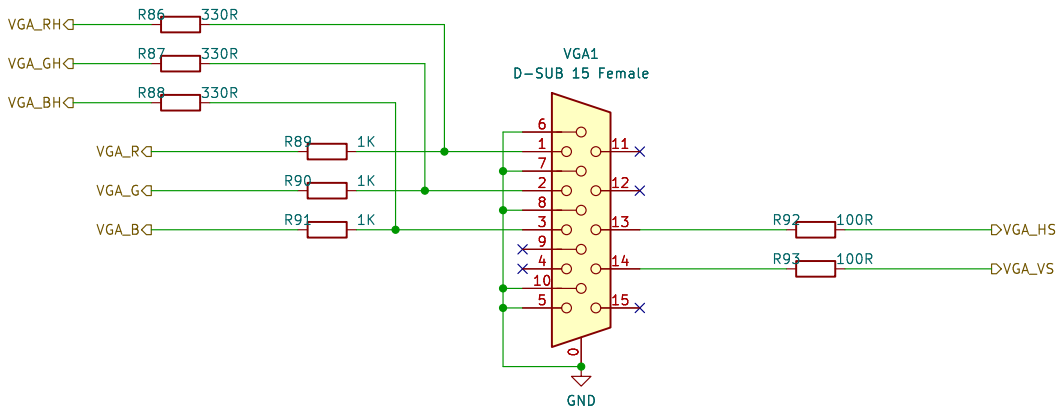
[picture p112: page 16]

https://github.com/xtremespb/frank

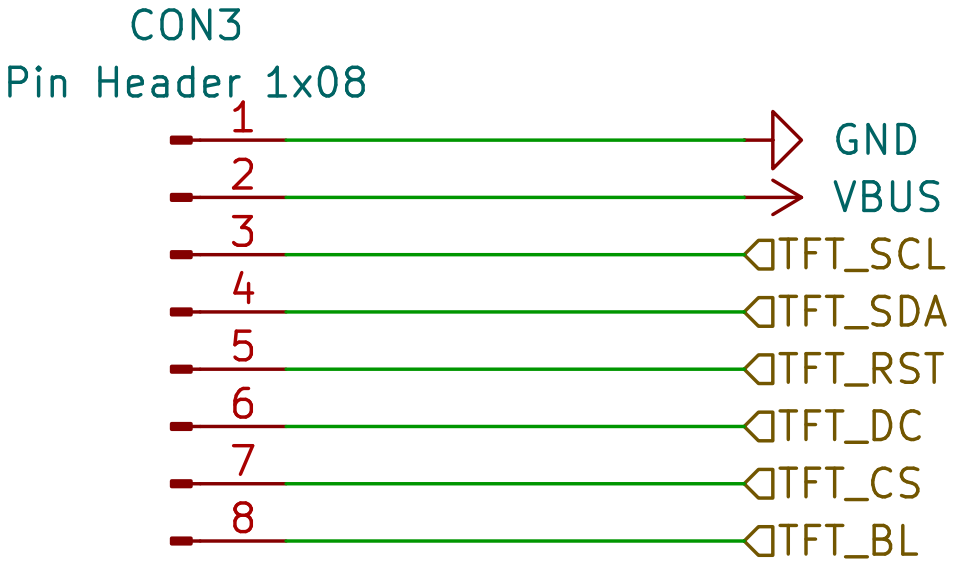
[picture p113: page 17]

https://github.com/xtremespb/frank

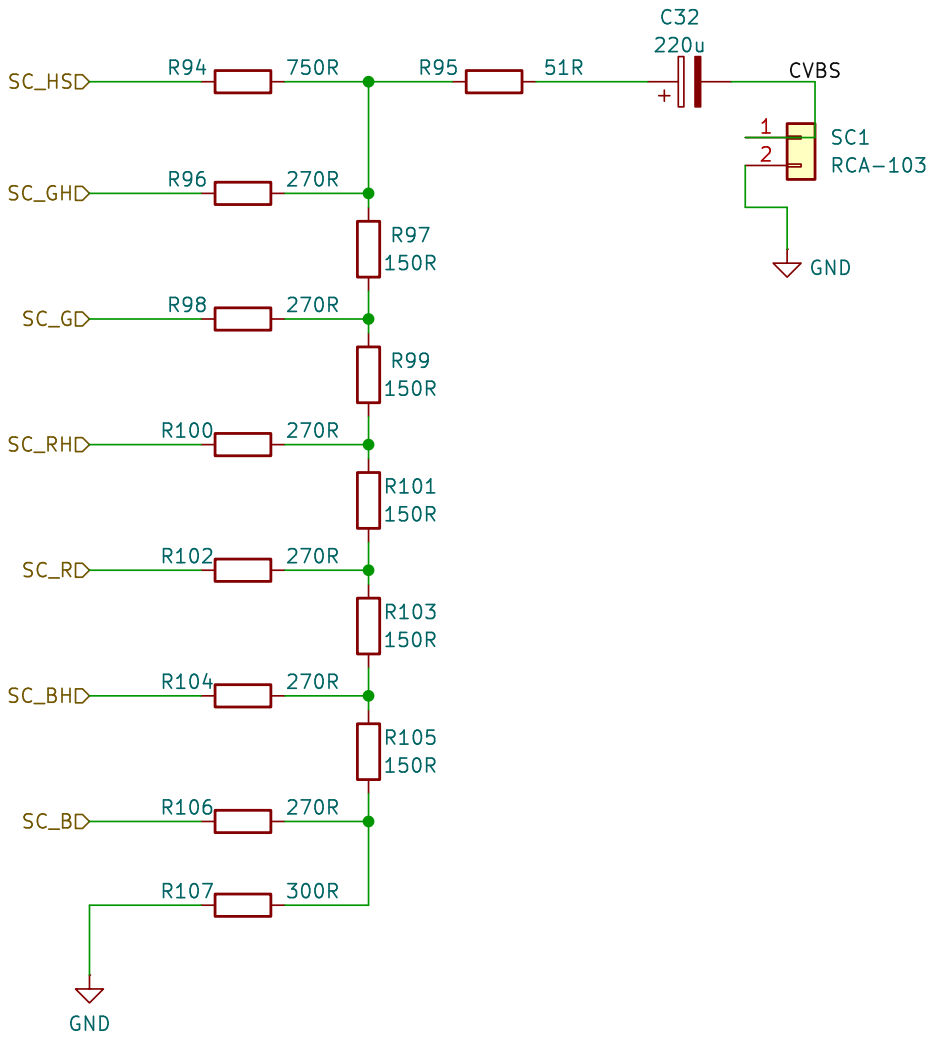
[picture p114: page 18]

https://github.com/xtremespb/frank

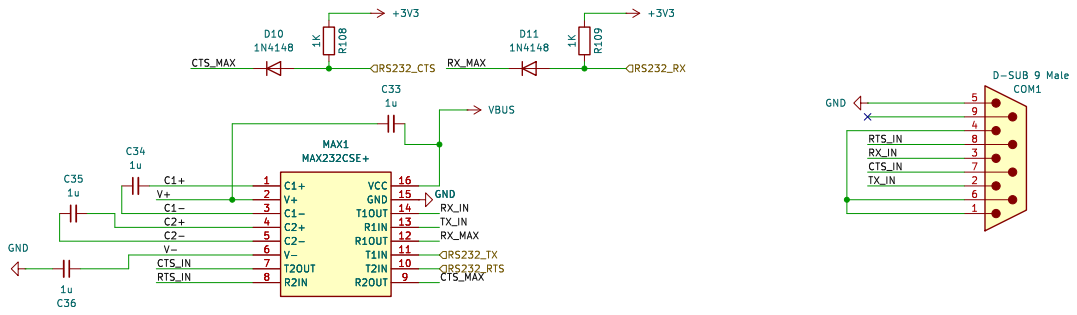
[picture p115: page 19]

https://github.com/xtremespb/frank
