xtremespb/frank/hardware/hdmi2vga/DOCS/hdmi2vgaP.pdf

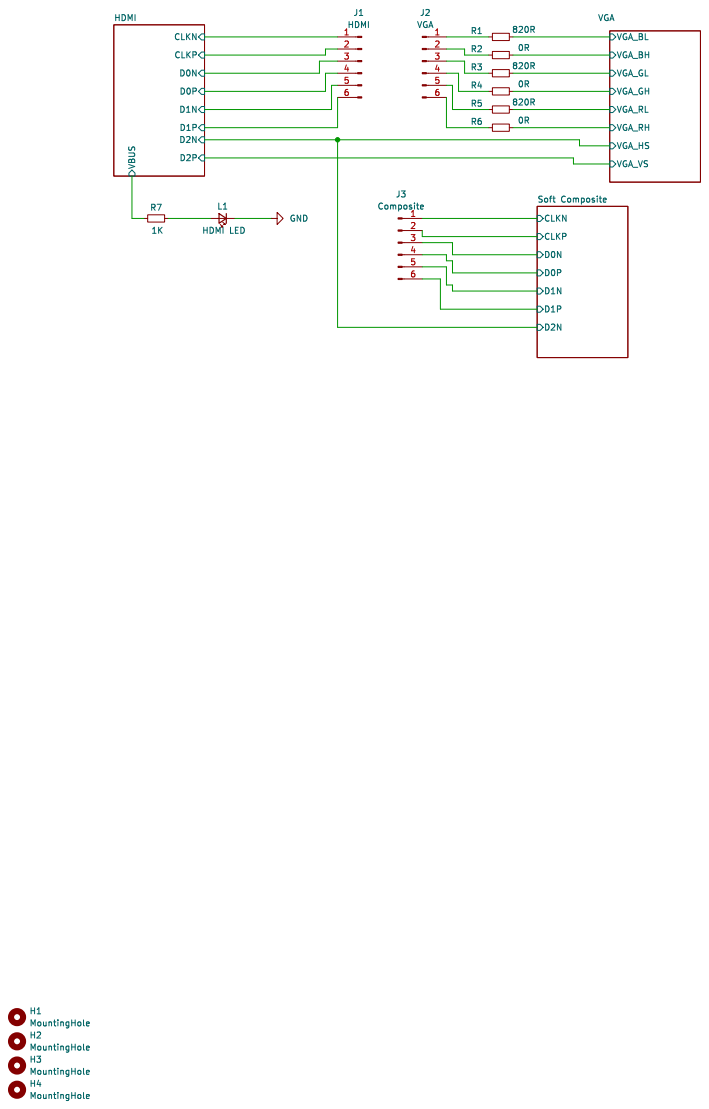
[picture p127: page 1]

https://github.com/xtremespb/frank

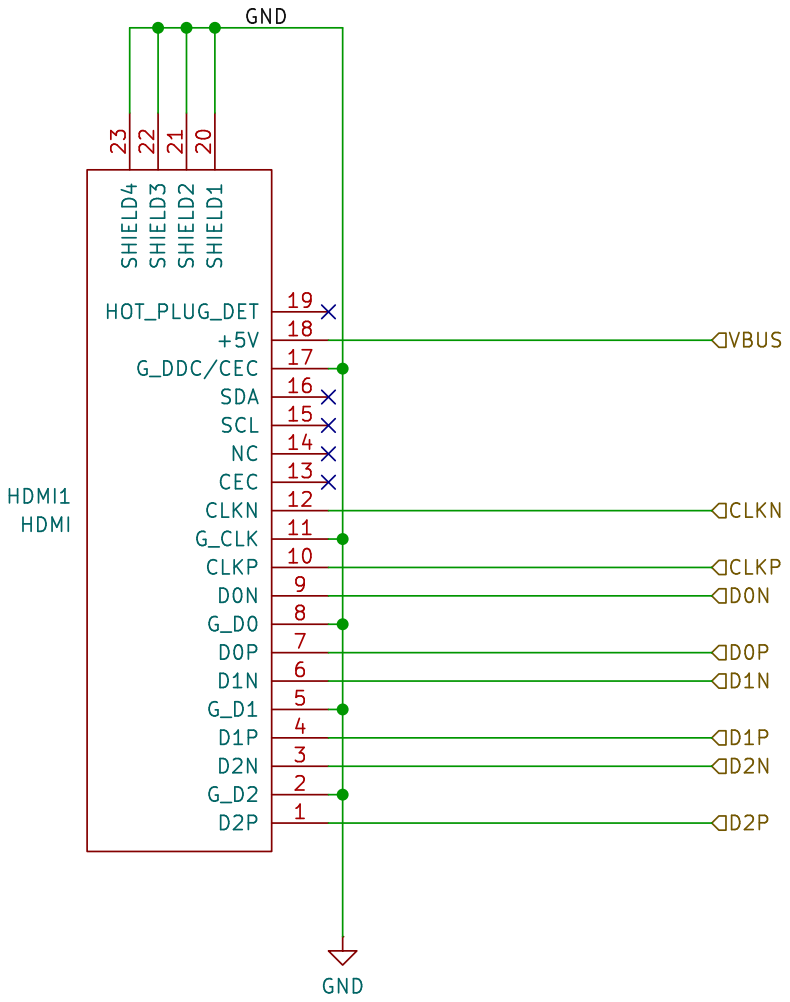
[picture p128: page 2]

https://github.com/xtremespb/frank

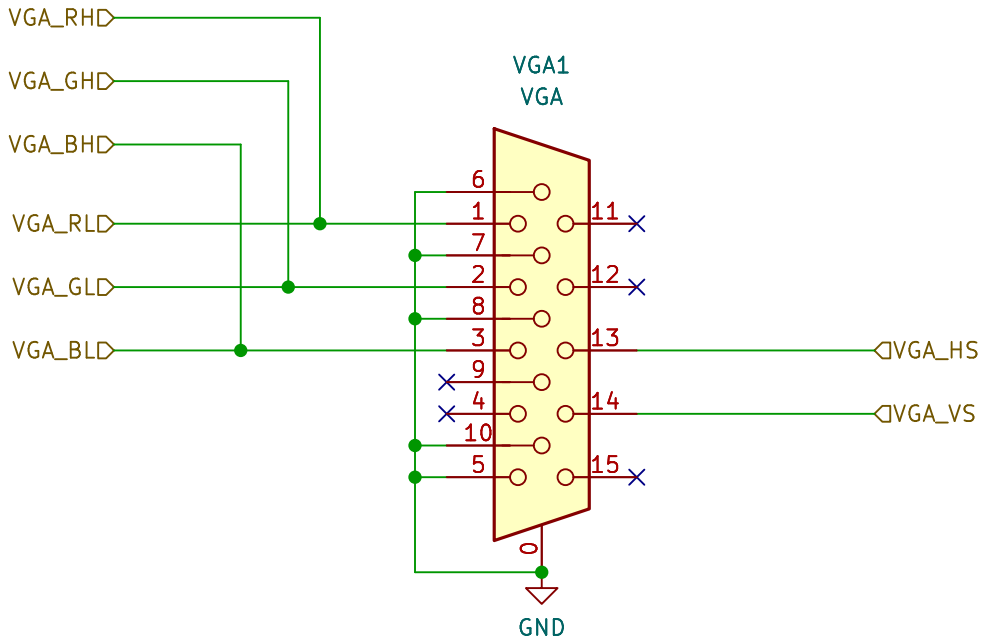
[picture p129: page 3]

https://github.com/xtremespb/frank

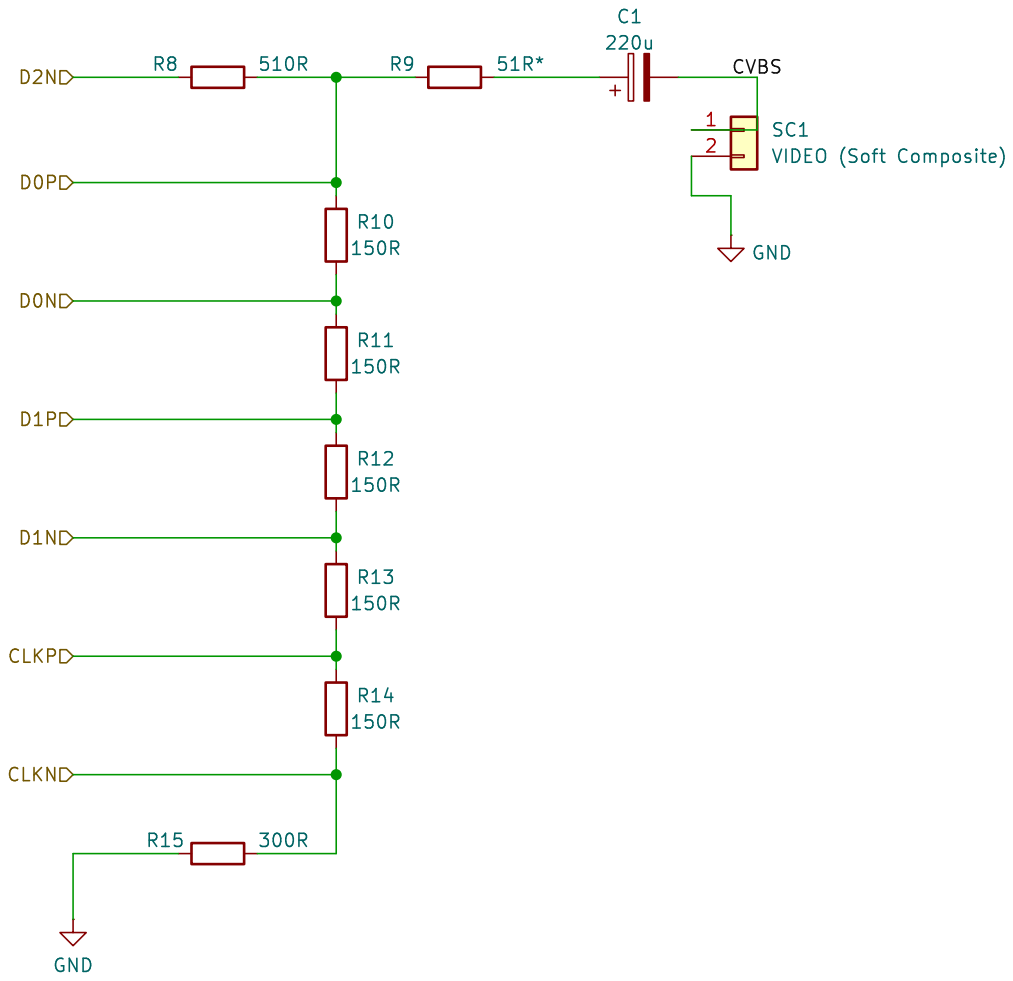
[picture p130: page 4]

https://github.com/xtremespb/frank
