xtremespb/frank/hardware/minifrank_rm1/DOCS/assembly.pdf

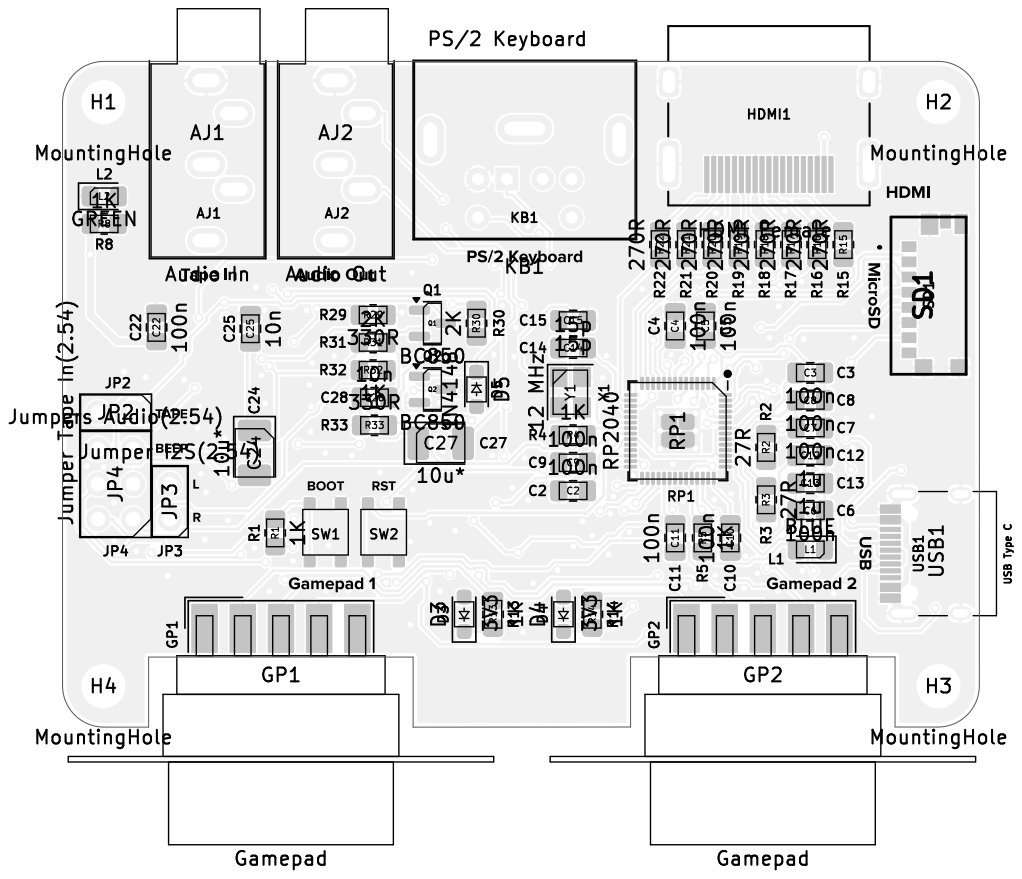
[picture p131: page 1]

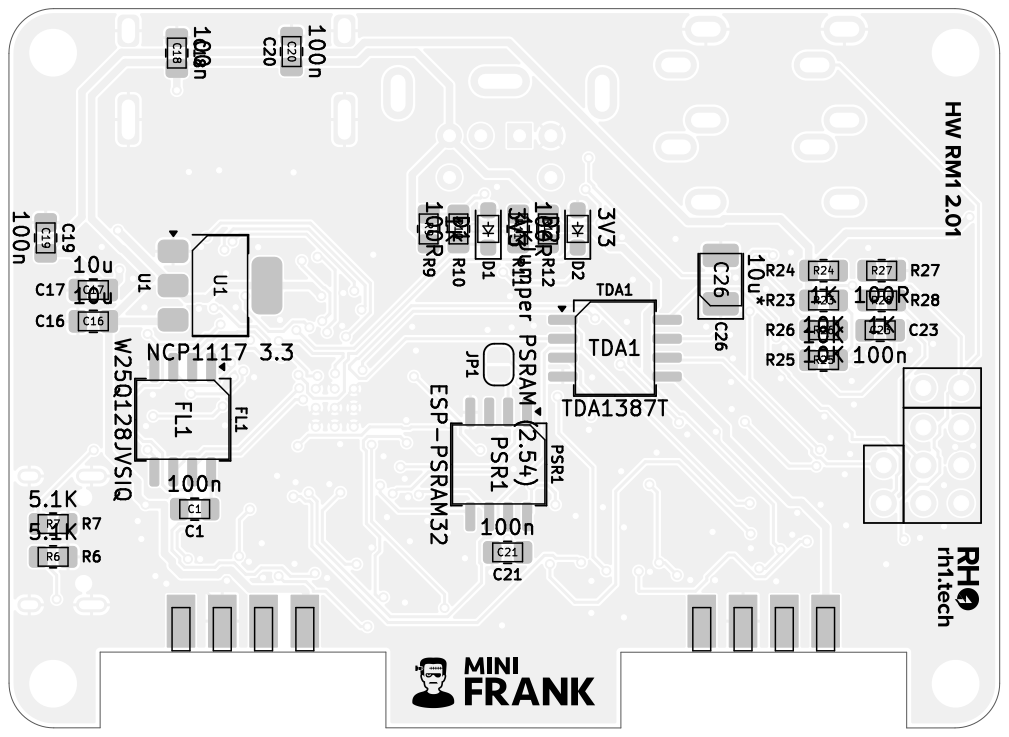
[picture p132: page 2]
